ArthurAdmiraal/EISFlowSensing/Documentation/Render/2_2Vtst_24V_Disturb_Screenshot.png

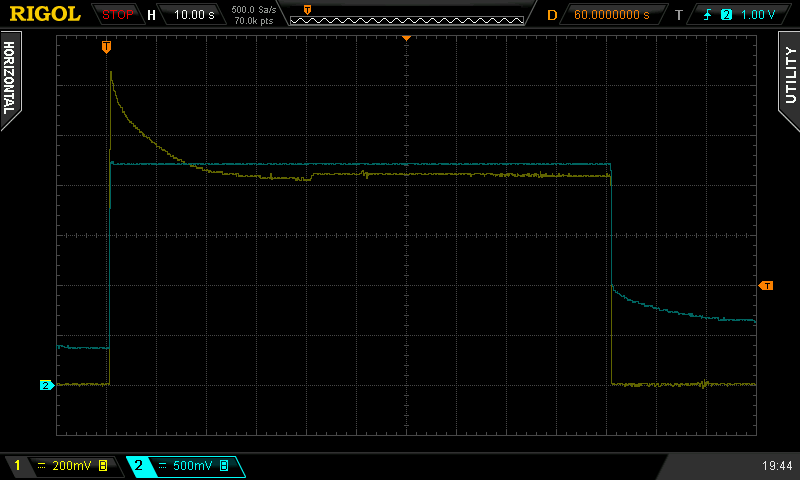
Documentation/Render/2_2Vtst_24V_Disturb_Screenshot.png
