ArthurAdmiraal/EISFlowSensing/Documentation/Render/2_2Vtst_24V_Normal_Screenshot.png

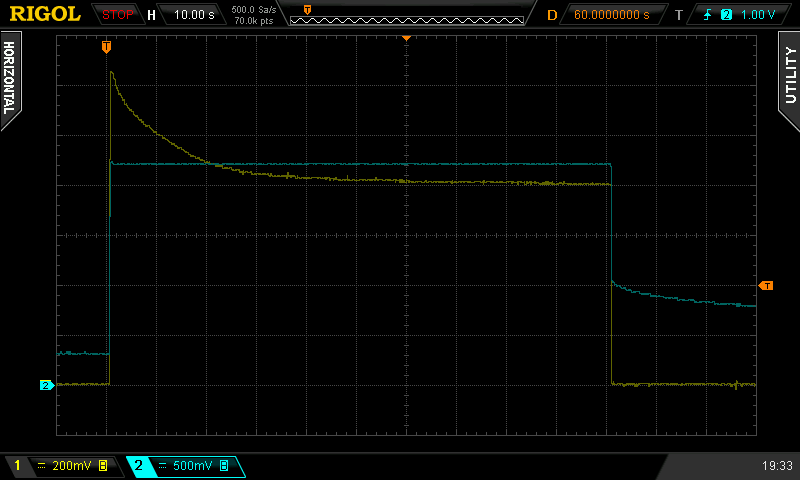
Documentation/Render/2_2Vtst_24V_Normal_Screenshot.png
