ArthurAdmiraal/EISFlowSensing/Documentation/Render/3DPrintGlueing.jpg

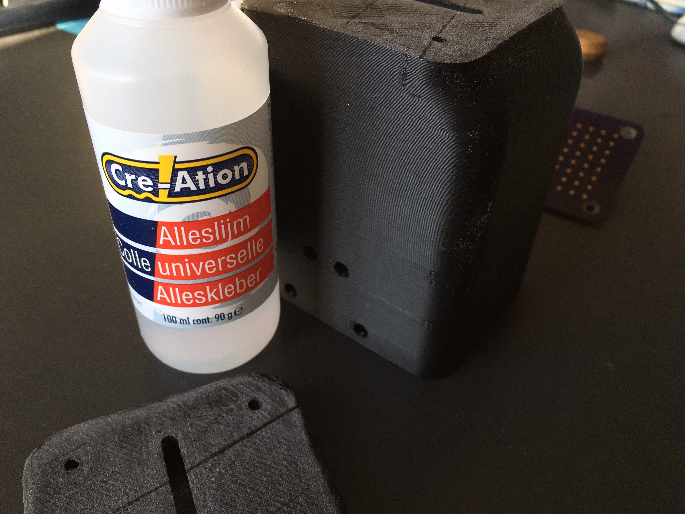
Documentation/Render/3DPrintGlueing.jpg
