ArthurAdmiraal/EISFlowSensing/Documentation/Render/DSC00186.jpg

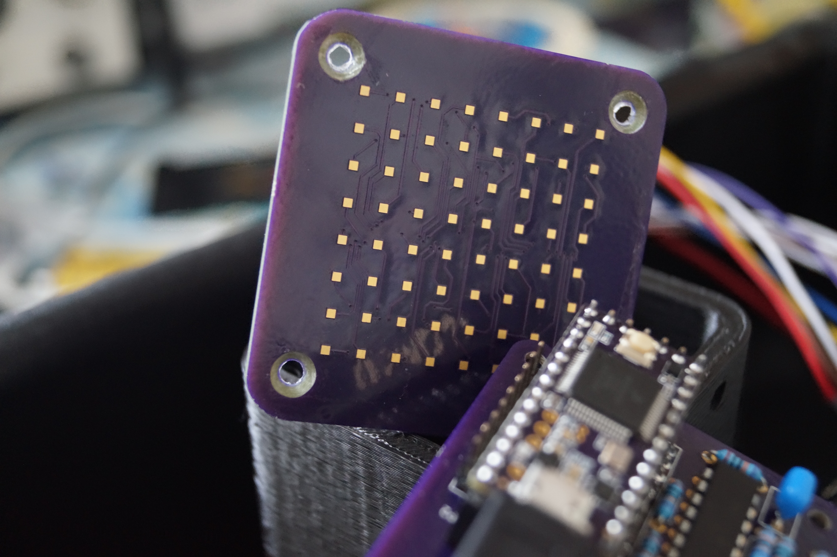
Documentation/Render/DSC00186.jpg
