ArthurAdmiraal/EISFlowSensing/Documentation/Render/DSC00188.jpg

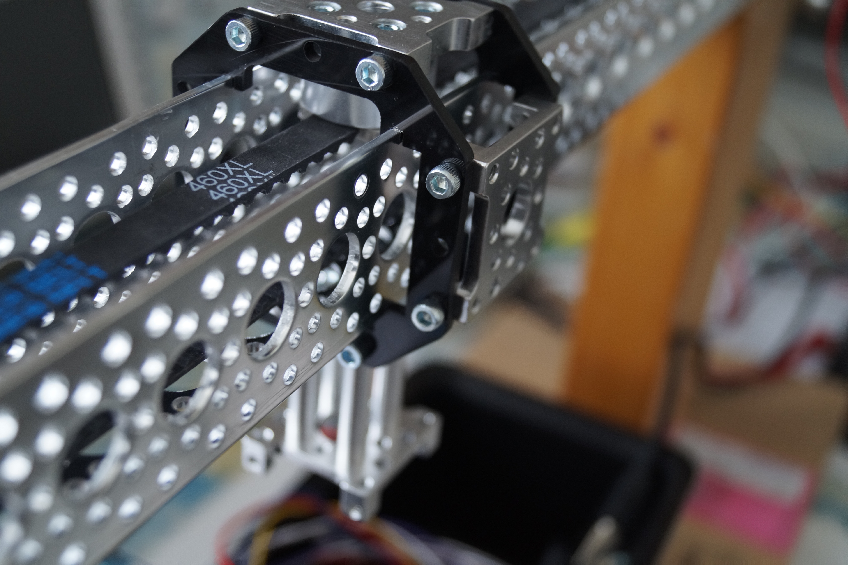
Documentation/Render/DSC00188.jpg
