ArthurAdmiraal/EISFlowSensing/Documentation/Render/ElectrodeAdjacent.png

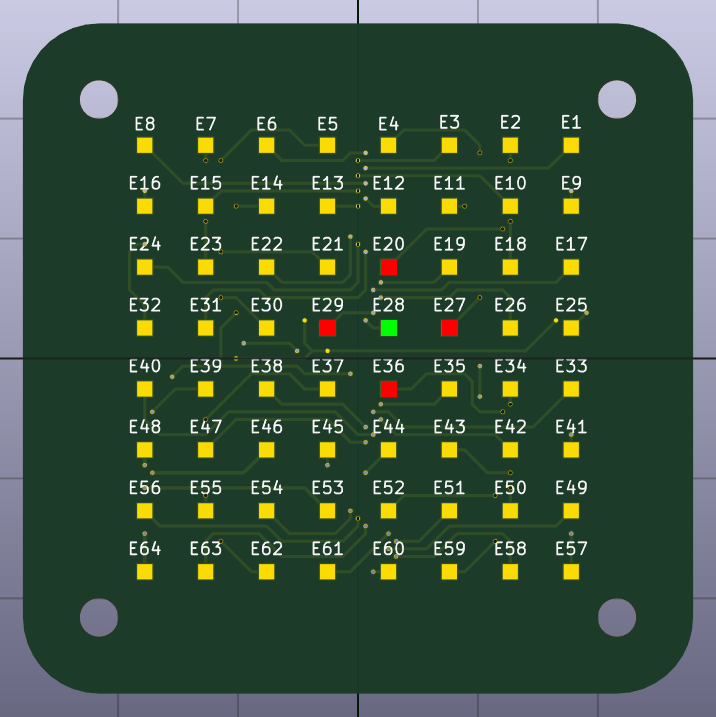
Documentation/Render/ElectrodeAdjacent.png
