ArthurAdmiraal/EISFlowSensing/Documentation/Render/ElectrodeChessBoard.svg.png

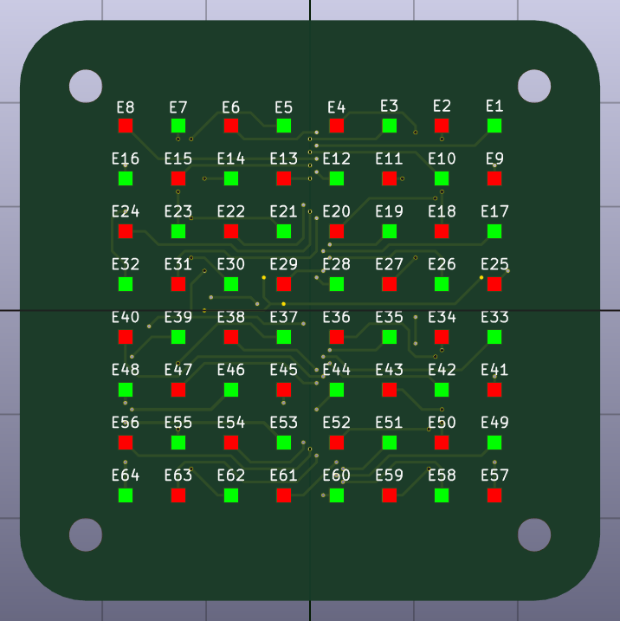
Documentation/Render/ElectrodeChessBoard.svg.png
