ArthurAdmiraal/EISFlowSensing/Documentation/Render/ElectrolyticSolution.png

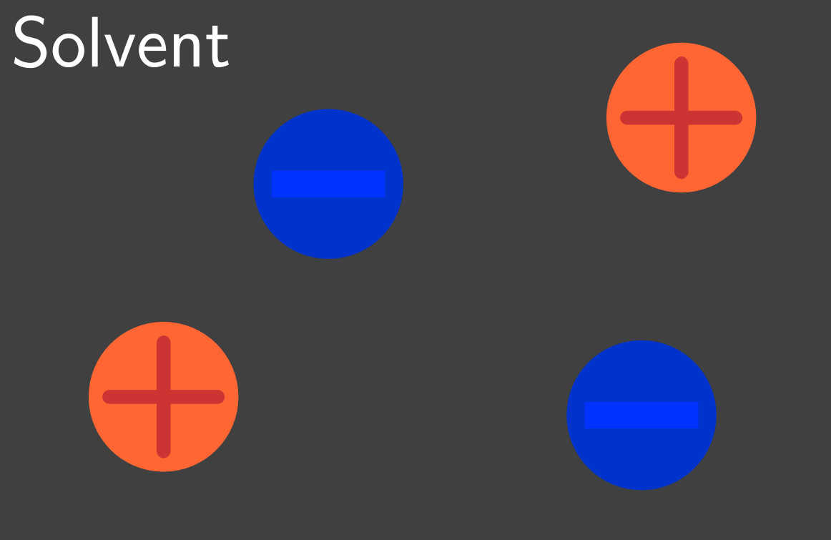
Documentation/Render/ElectrolyticSolution.png
