ArthurAdmiraal/EISFlowSensing/Documentation/Render/EquivalentCircuit.png

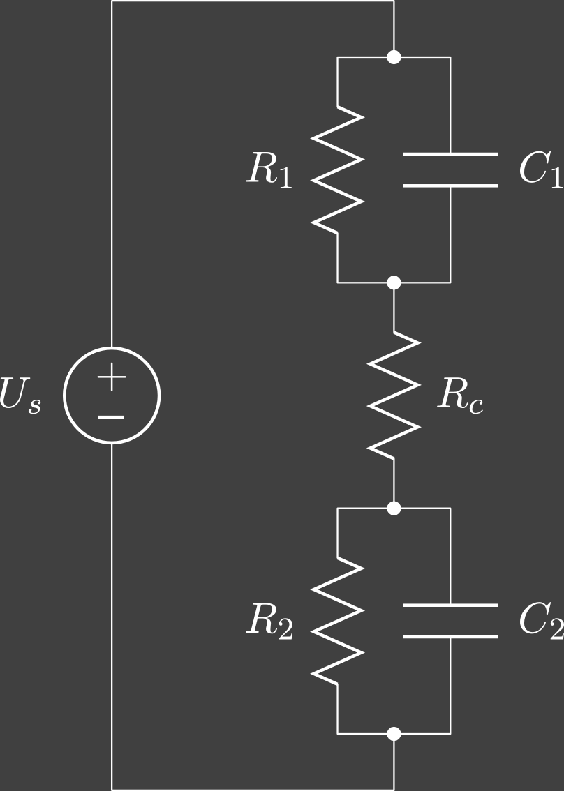
Documentation/Render/EquivalentCircuit.png
