ArthurAdmiraal/EISFlowSensing/Documentation/Render/FaradaicCurrent.png

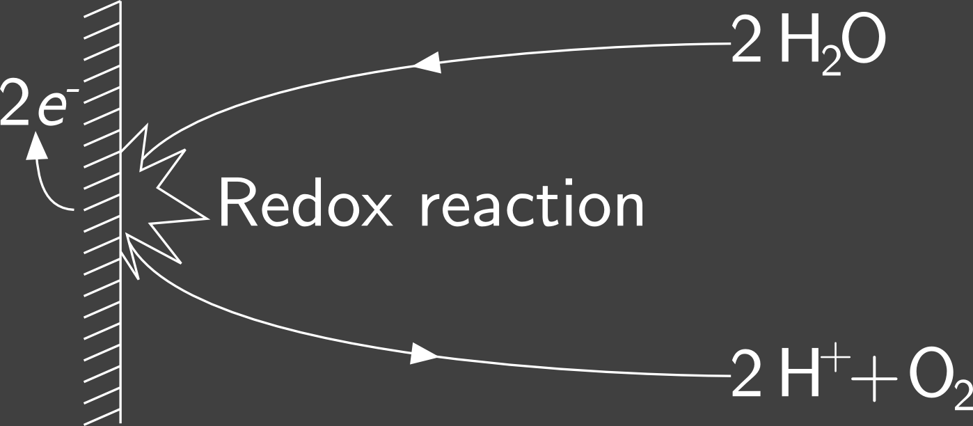
Documentation/Render/FaradaicCurrent.png
