ArthurAdmiraal/EISFlowSensing/Documentation/Render/GrubScrew.jpg

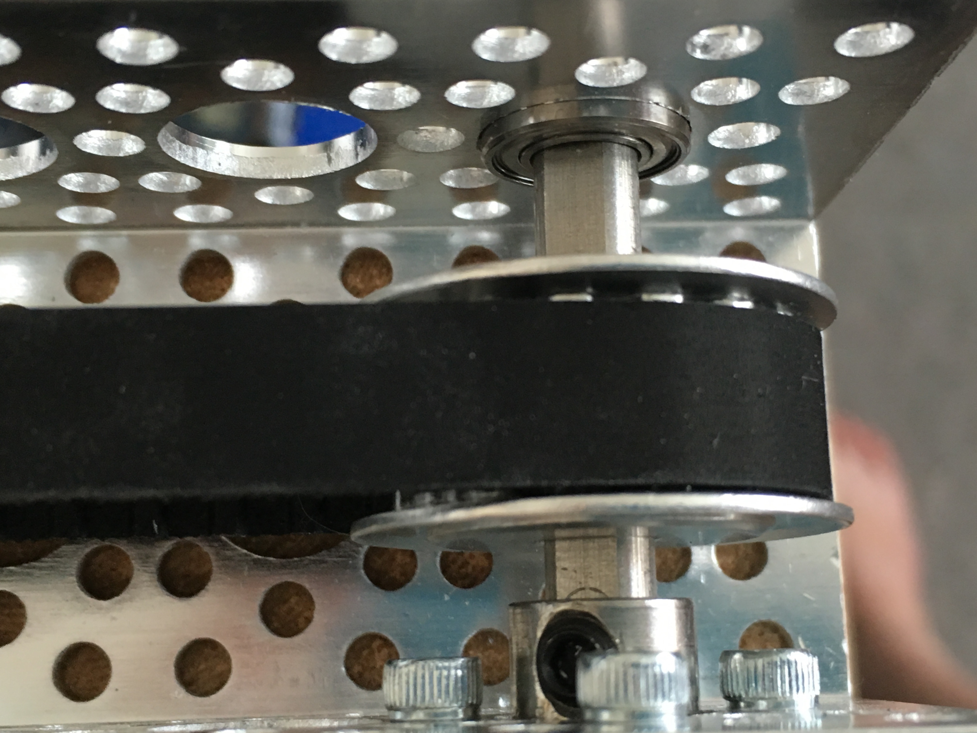
Documentation/Render/GrubScrew.jpg
