ArthurAdmiraal/EISFlowSensing/Documentation/Render/IMG_5456.jpg

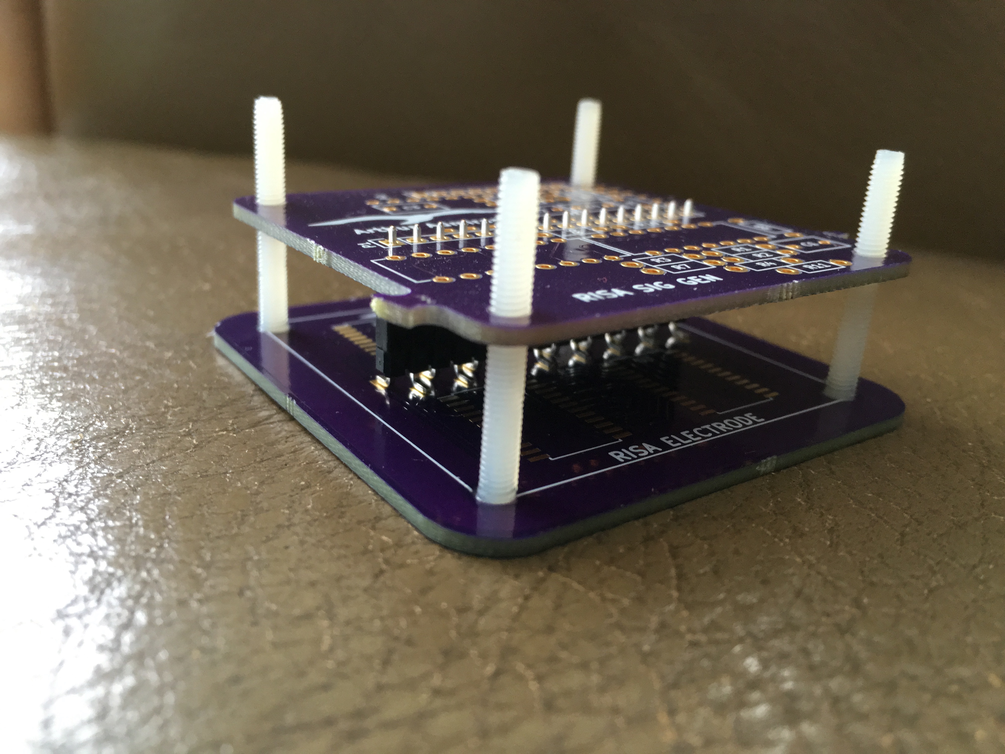
Documentation/Render/IMG_5456.jpg
