ArthurAdmiraal/EISFlowSensing/Documentation/Render/IMG_5630.JPG

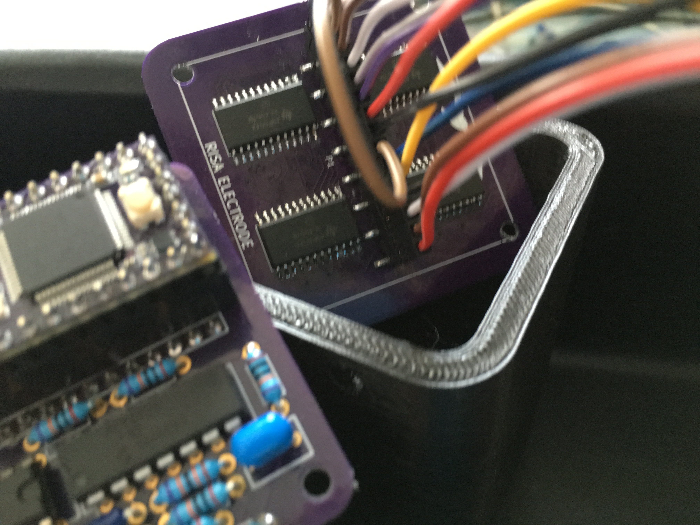
Documentation/Render/IMG_5630.JPG
