ArthurAdmiraal/EISFlowSensing/Documentation/Render/LimitSwitch.jpg

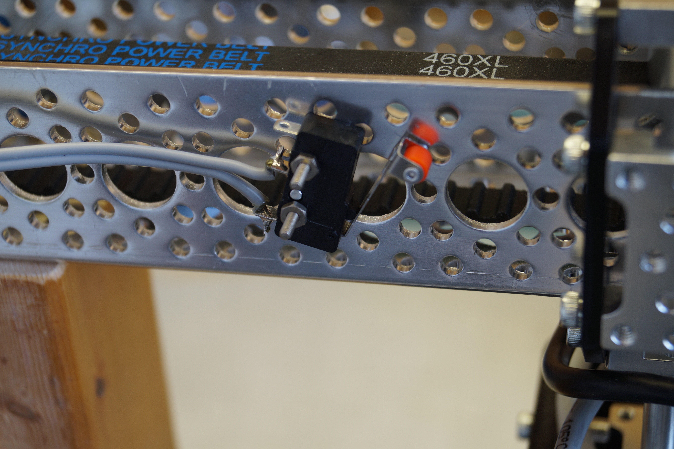
Documentation/Render/LimitSwitch.jpg
