ArthurAdmiraal/EISFlowSensing/Documentation/Render/LimitSwitchCableHotGlue.jpg

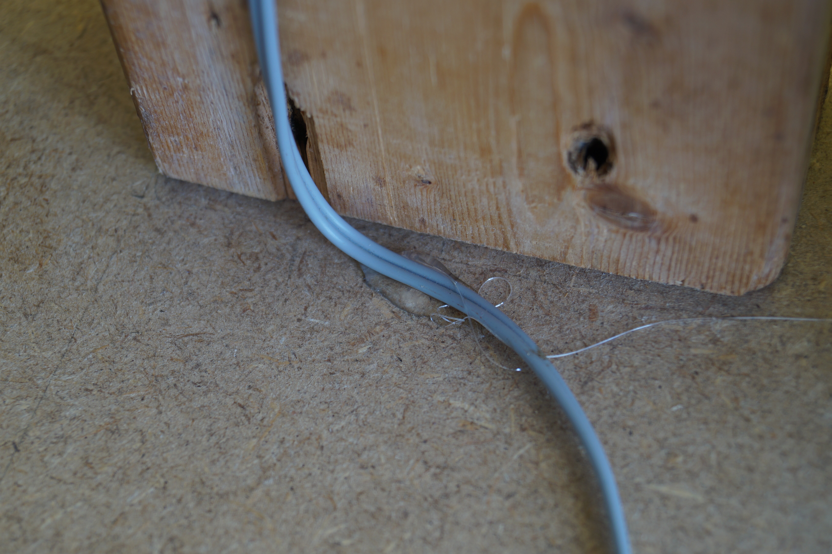
Documentation/Render/LimitSwitchCableHotGlue.jpg
