ArthurAdmiraal/EISFlowSensing/Documentation/Render/ORingUnfit.jpg

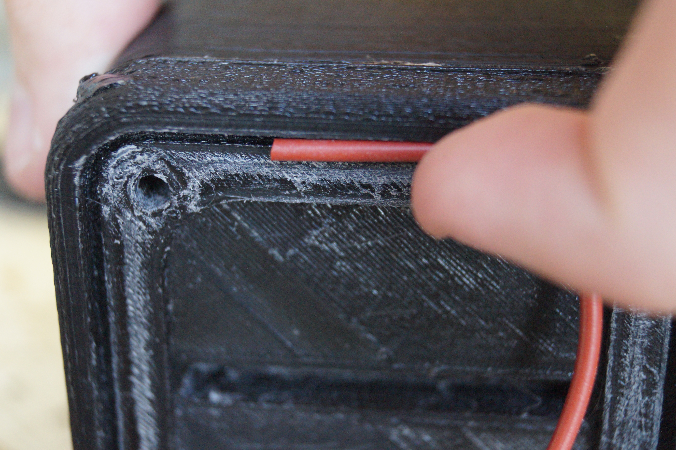
Documentation/Render/ORingUnfit.jpg
