ArthurAdmiraal/EISFlowSensing/Documentation/Render/RISA_Case_CentralShaft.png

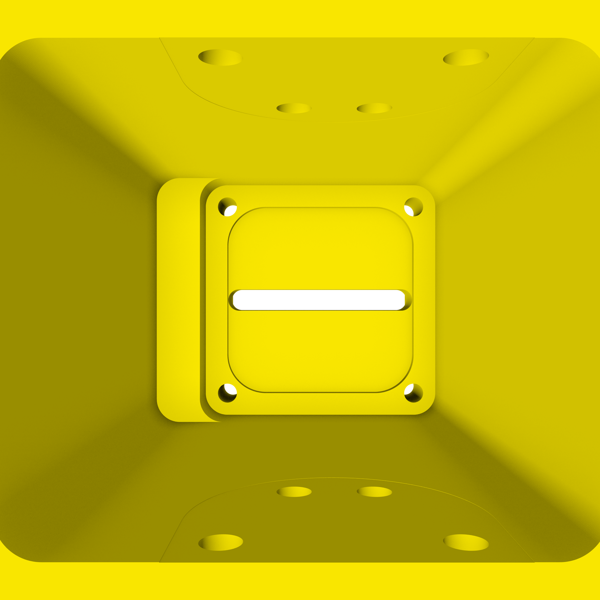
Documentation/Render/RISA_Case_CentralShaft.png
