ArthurAdmiraal/EISFlowSensing/Documentation/Render/RISA_Case_ElectrodeMount.png

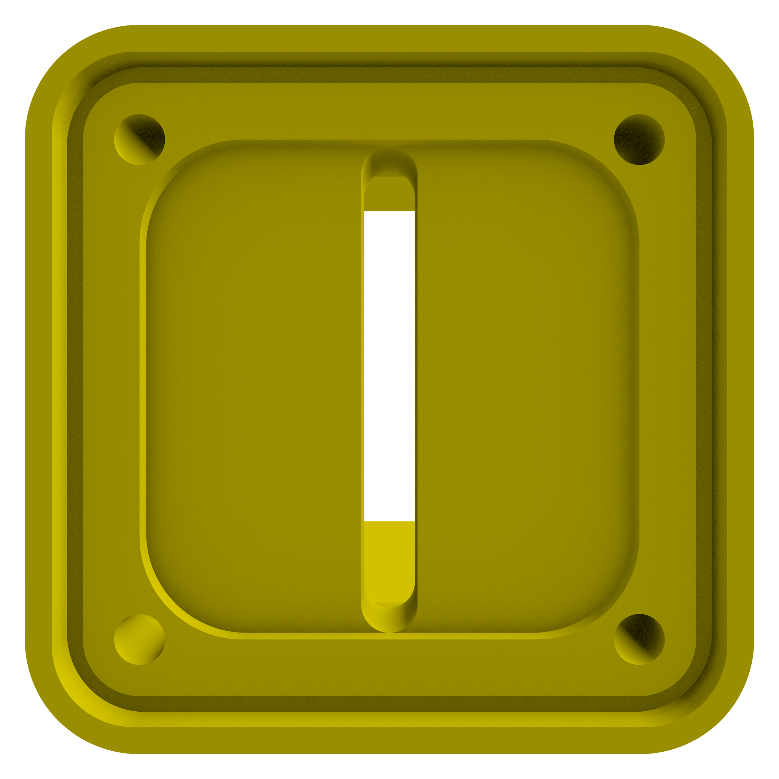
Documentation/Render/RISA_Case_ElectrodeMount.png
