ArthurAdmiraal/EISFlowSensing/Documentation/Render/RISA_Case_full.png

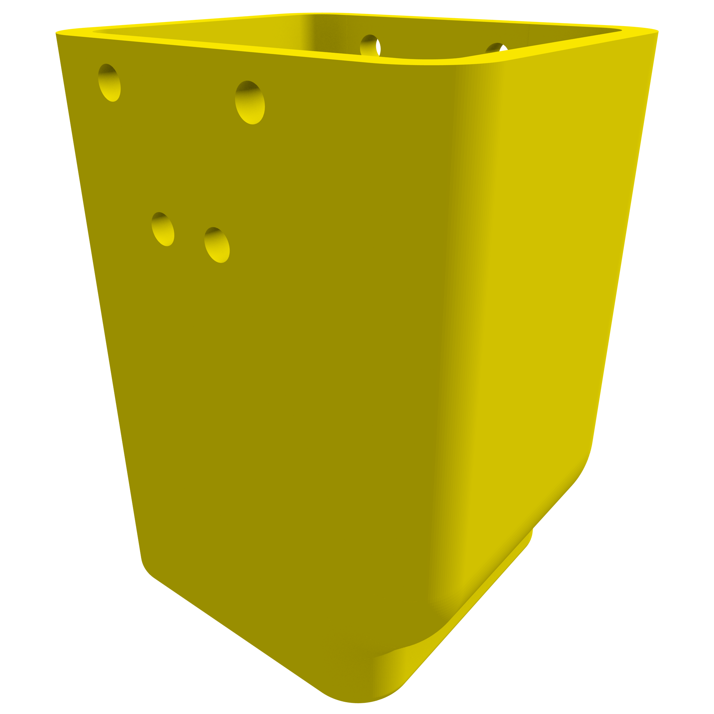
Documentation/Render/RISA_Case_full.png
