ArthurAdmiraal/EISFlowSensing/Documentation/Render/RISA_Case_MountingHoles.png

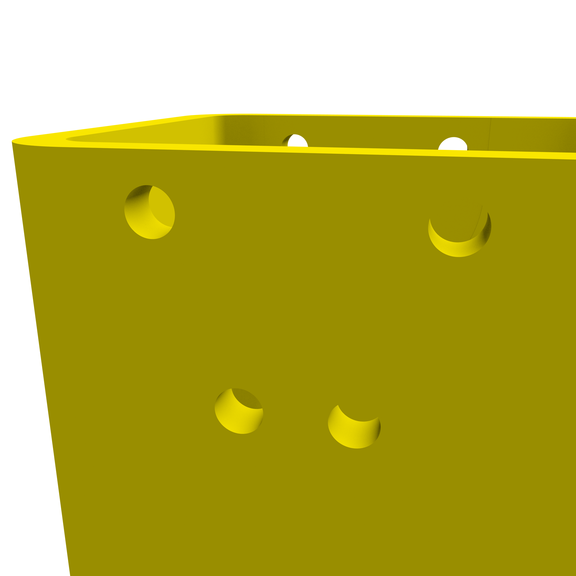
Documentation/Render/RISA_Case_MountingHoles.png
