ArthurAdmiraal/EISFlowSensing/Documentation/Render/RisaSliderInterface.jpg

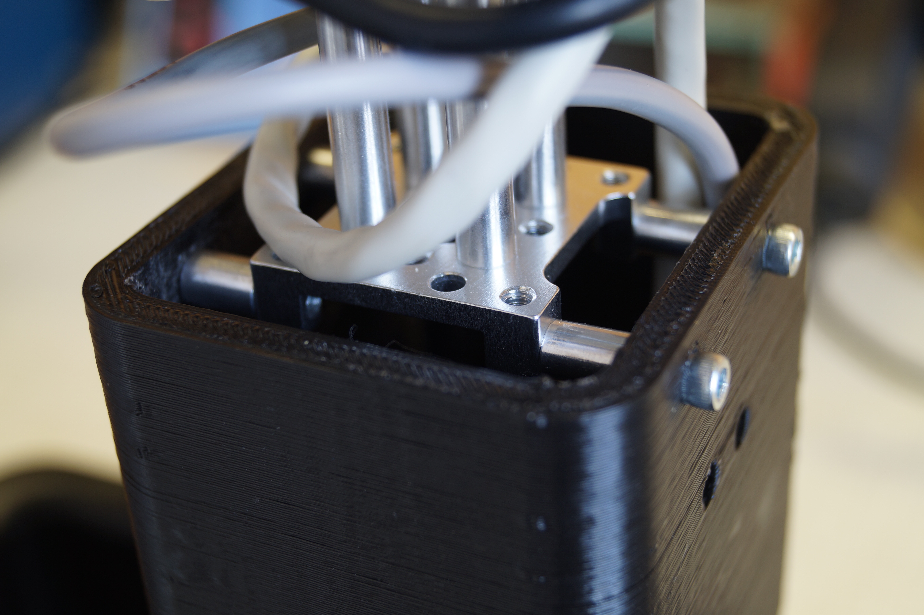
Documentation/Render/RisaSliderInterface.jpg
