ArthurAdmiraal/EISFlowSensing/Documentation/Render/SigGenCurrentBuffer.png

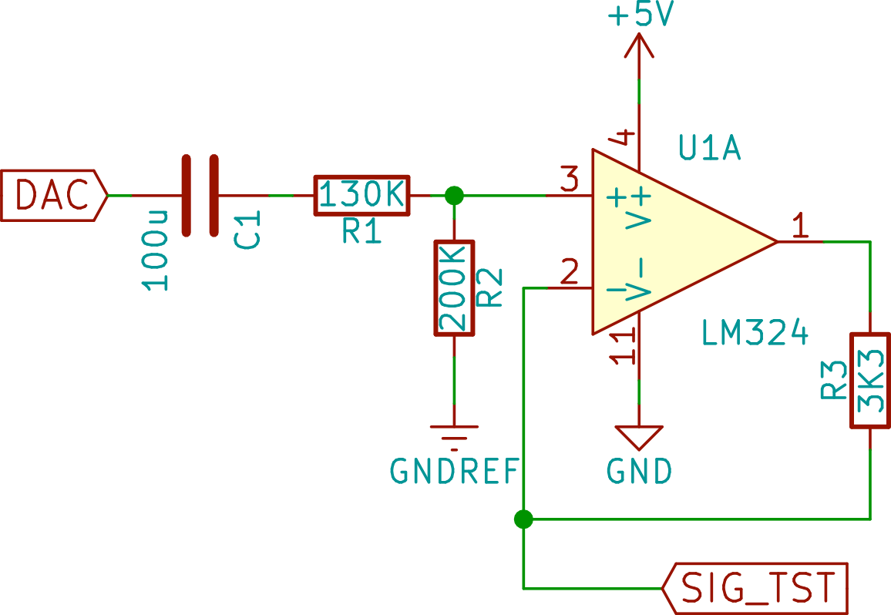
Documentation/Render/SigGenCurrentBuffer.png
