ArthurAdmiraal/EISFlowSensing/Documentation/Render/SigGenFinal.png

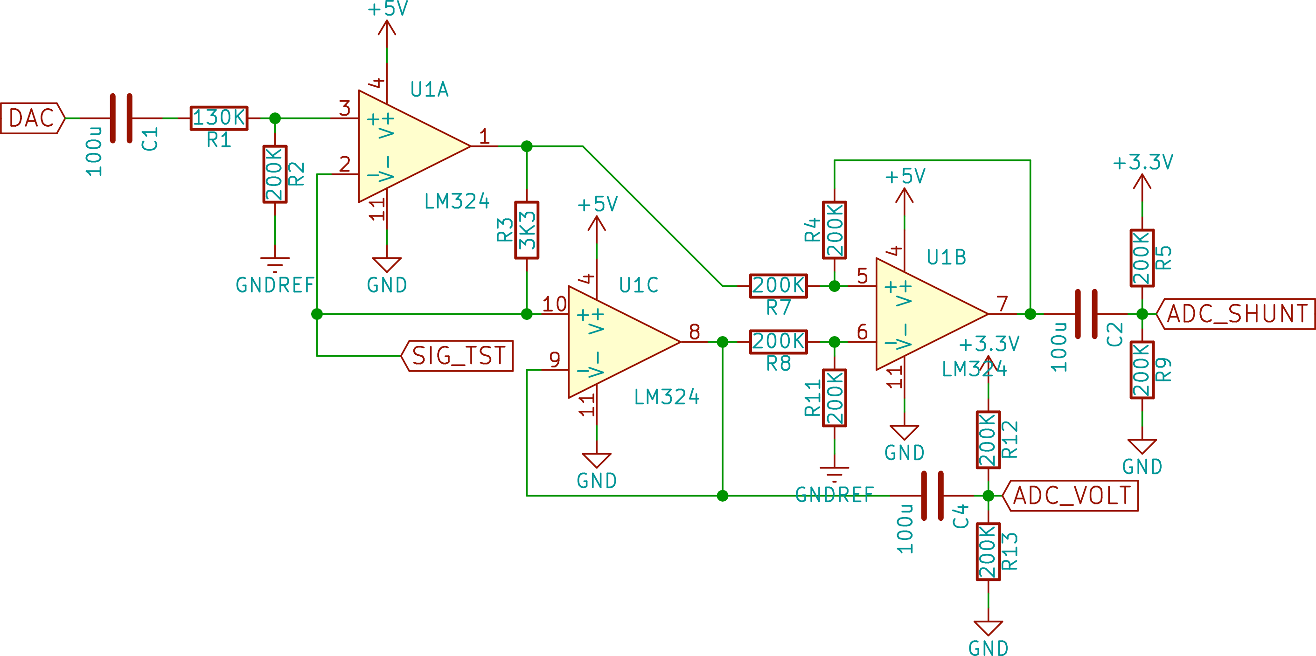
Documentation/Render/SigGenFinal.png
