ArthurAdmiraal/EISFlowSensing/Documentation/Render/SigGenInputBiasing.png

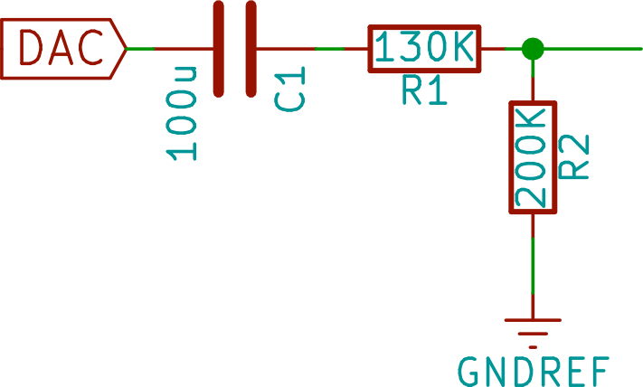
Documentation/Render/SigGenInputBiasing.png
