ArthurAdmiraal/EISFlowSensing/Documentation/Render/SigGenMultiplexer.png

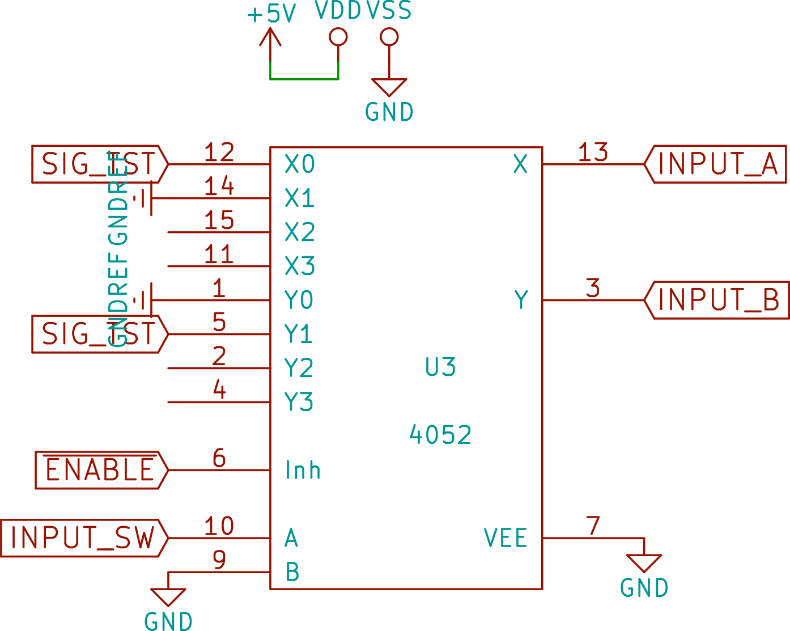
Documentation/Render/SigGenMultiplexer.png
