ArthurAdmiraal/EISFlowSensing/Documentation/Render/SigGenTeensy.png

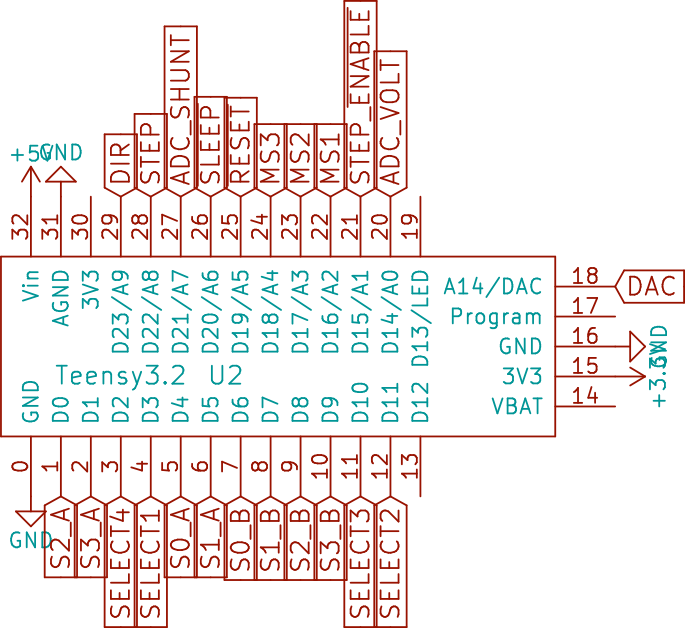
Documentation/Render/SigGenTeensy.png
