ArthurAdmiraal/EISFlowSensing/Documentation/Render/SigGenVirtualGround.png

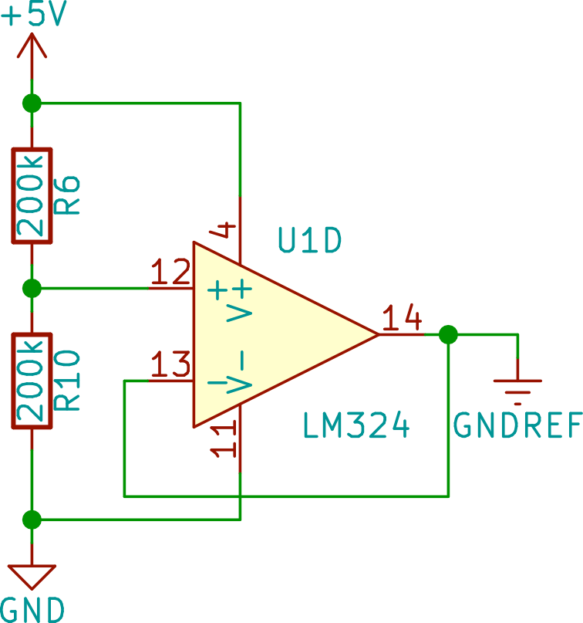
Documentation/Render/SigGenVirtualGround.png
