ArthurAdmiraal/EISFlowSensing/Documentation/Render/Slider.jpg

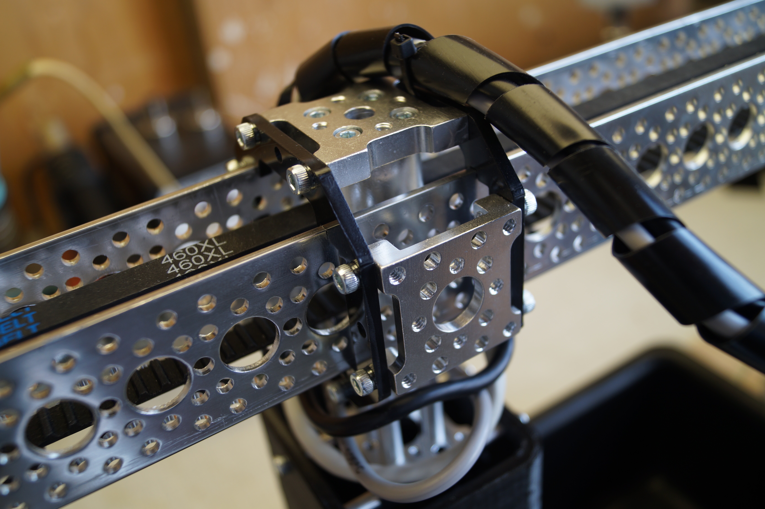
Documentation/Render/Slider.jpg
