ArthurAdmiraal/EISFlowSensing/Documentation/Render/SliderBaseInterface.jpg

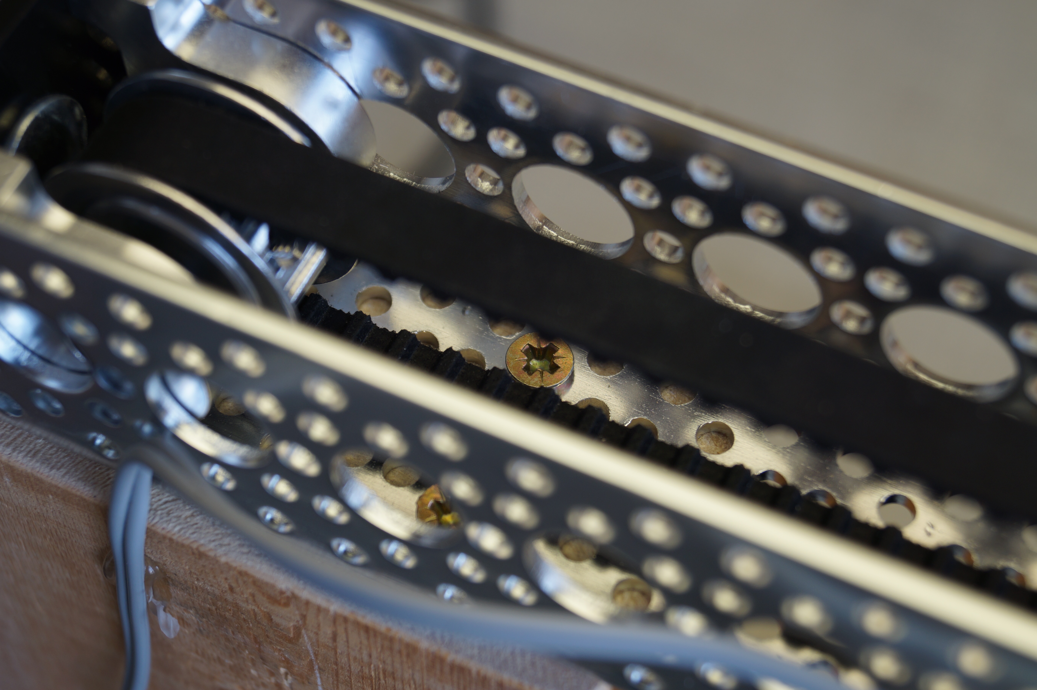
Documentation/Render/SliderBaseInterface.jpg
