ArthurAdmiraal/EISFlowSensing/Documentation/Render/StepperMotor.jpg

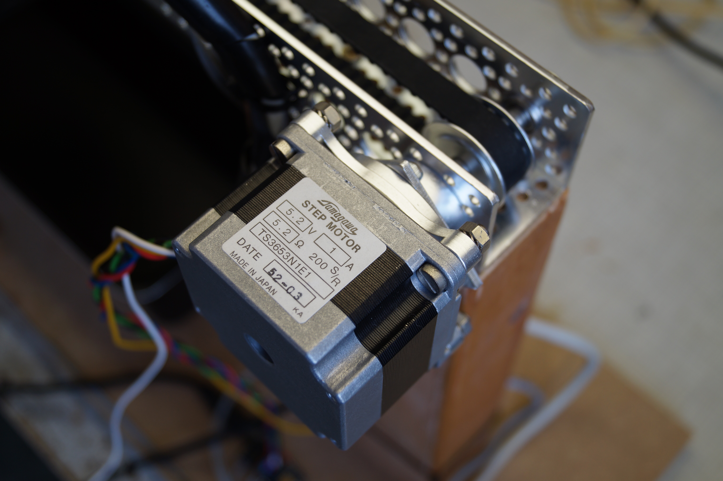
Documentation/Render/StepperMotor.jpg
