ArthurAdmiraal/EISFlowSensing/Documentation/Render/StepperMotorDriver.jpg

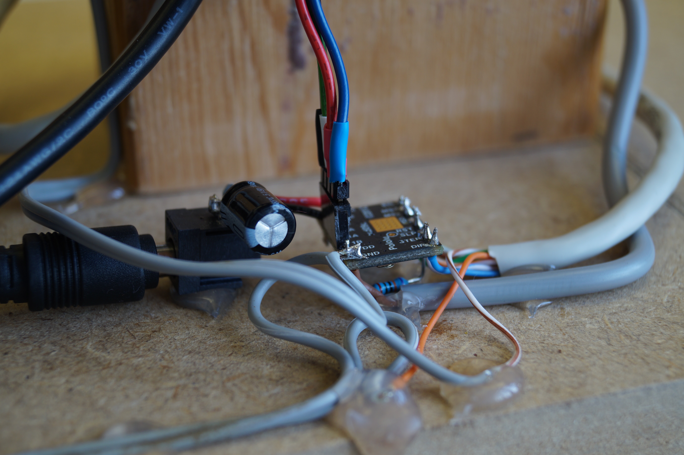
Documentation/Render/StepperMotorDriver.jpg
