ArthurAdmiraal/EISFlowSensing/Documentation/Render/WeightMonitoring.png

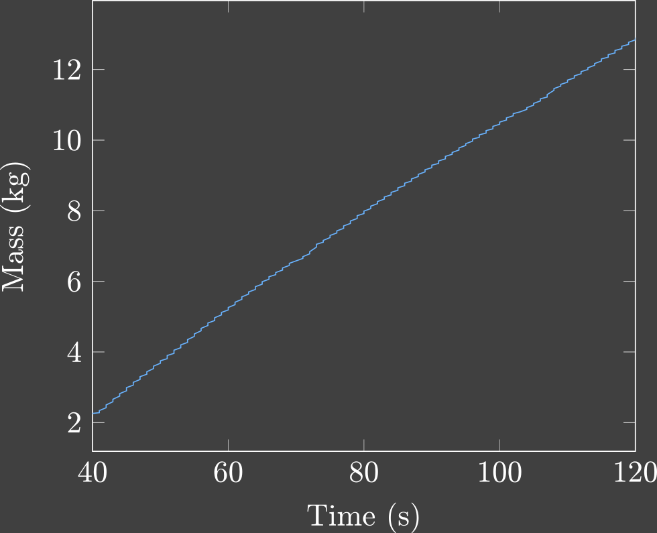
Documentation/Render/WeightMonitoring.png
