ArthurAdmiraal/EISFlowSensing/Documentation/Source/BodgeWire.jpg

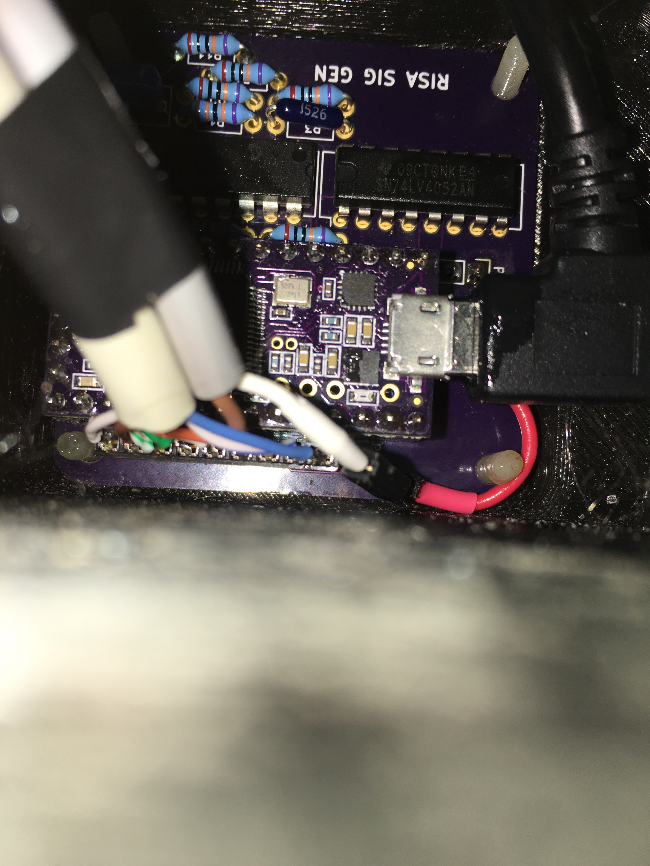
Documentation/Source/BodgeWire.jpg
