ArthurAdmiraal/EISFlowSensing/Documentation/Build_instructions/Step1.PNG

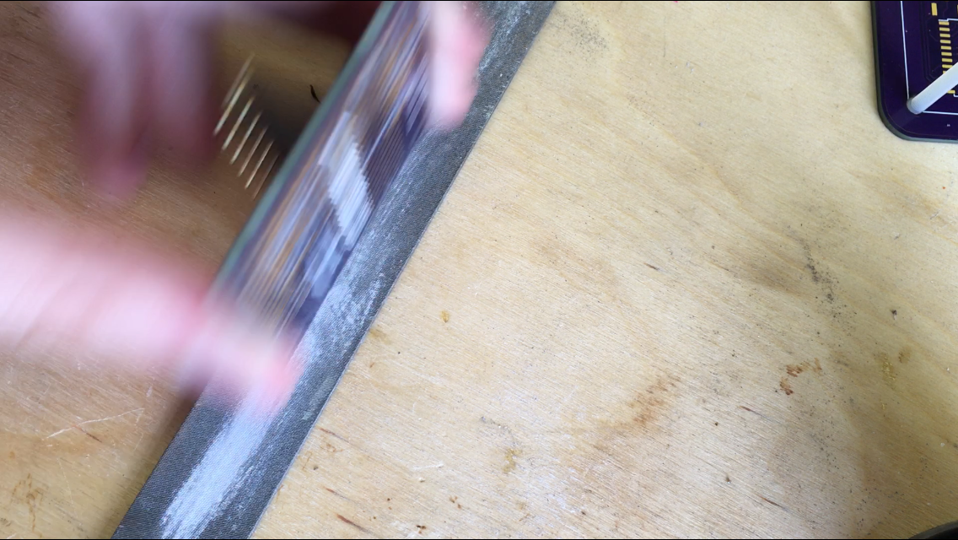
Documentation/Build_instructions/Step1.PNG
