ArthurAdmiraal/EISFlowSensing/Documentation/Build_instructions/Step1_0.PNG

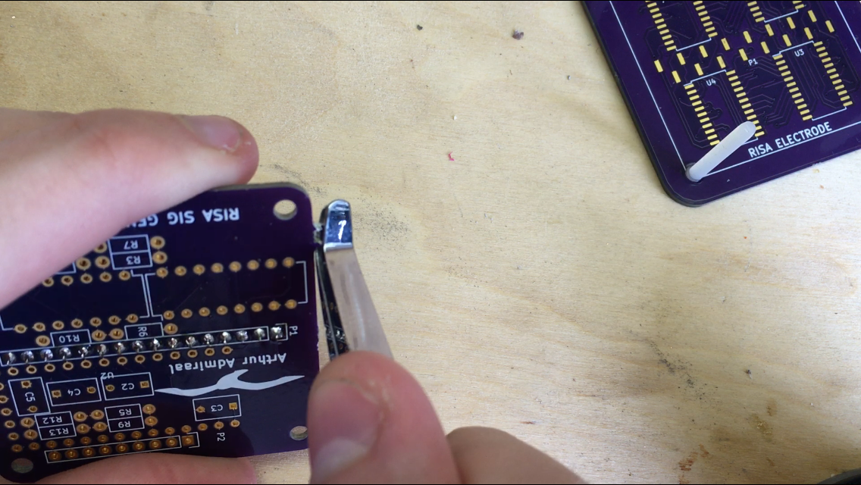
Documentation/Build_instructions/Step1_0.PNG
