ArthurAdmiraal/EISFlowSensing/Documentation/Build_instructions/Step2.PNG

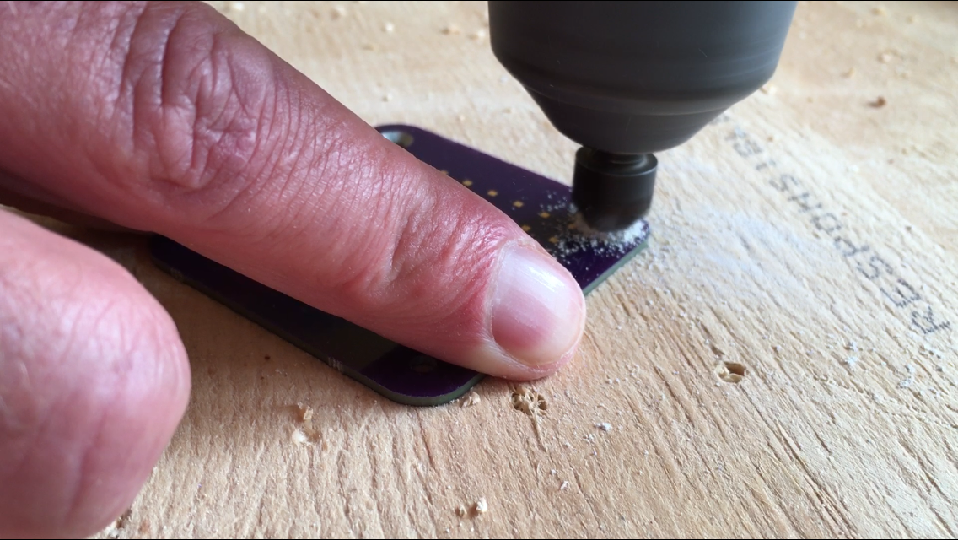
Documentation/Build_instructions/Step2.PNG
