ArthurAdmiraal/EISFlowSensing/Documentation/Build_instructions/Step3_1.PNG

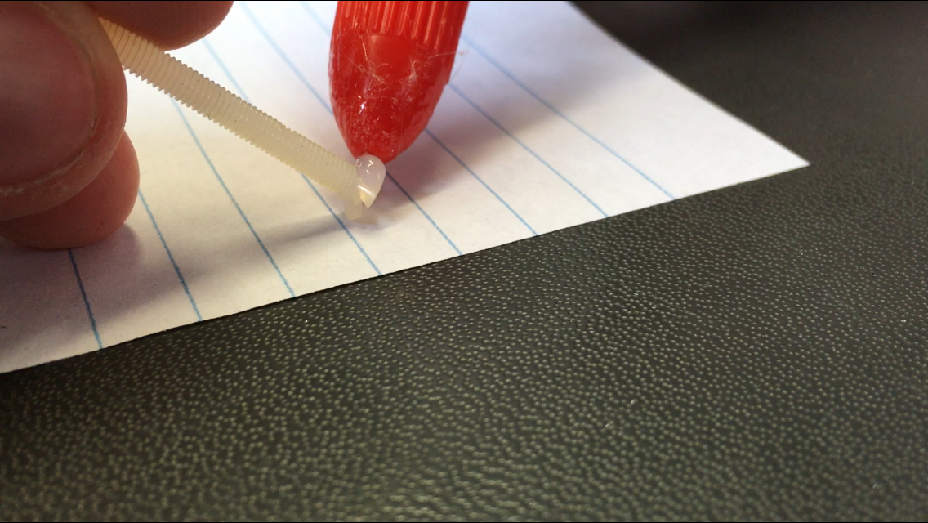
Documentation/Build_instructions/Step3_1.PNG
