ArthurAdmiraal/EISFlowSensing/Documentation/Build_instructions/Step3_2.PNG

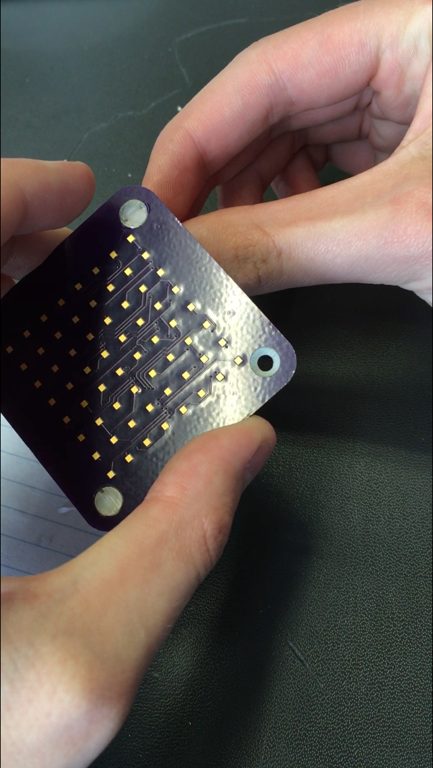
Documentation/Build_instructions/Step3_2.PNG
