ArthurAdmiraal/EISFlowSensing/Documentation/Build_instructions/Step3_3.JPG

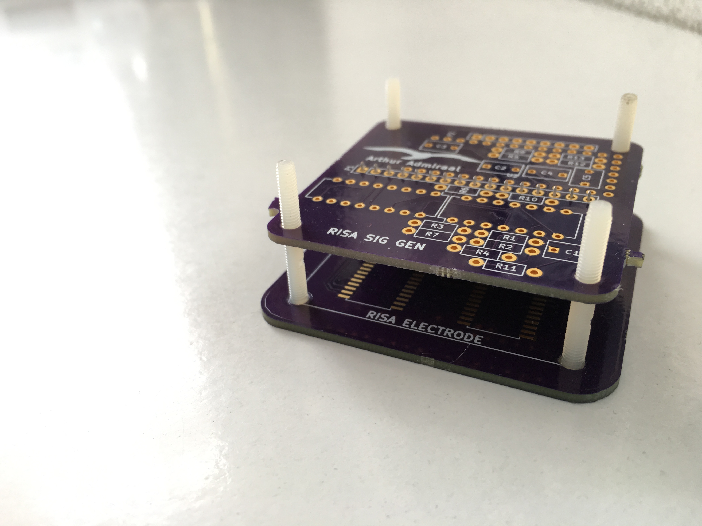
Documentation/Build_instructions/Step3_3.JPG
