ArthurAdmiraal/EISFlowSensing/Documentation/Build_instructions/Step4_1.PNG

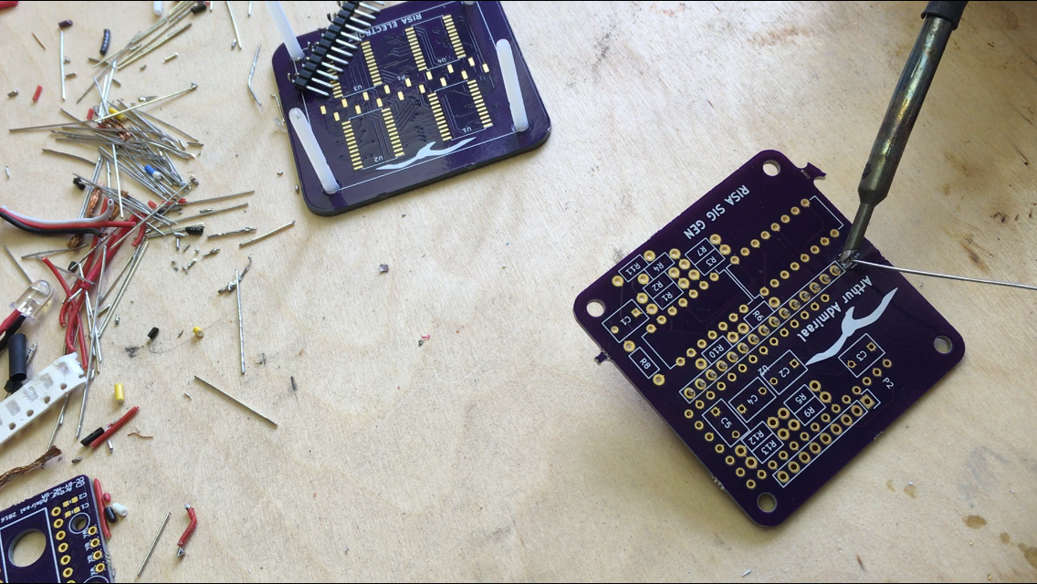
Documentation/Build_instructions/Step4_1.PNG
