ArthurAdmiraal/EISFlowSensing/Documentation/Build_instructions/Step4_2.PNG

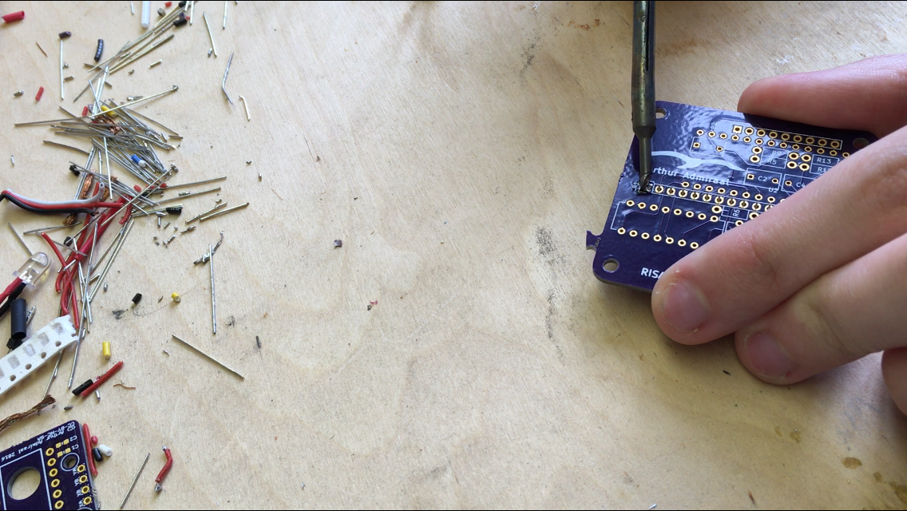
Documentation/Build_instructions/Step4_2.PNG
