ArthurAdmiraal/EISFlowSensing/Documentation/Build_instructions/Step4_3.PNG

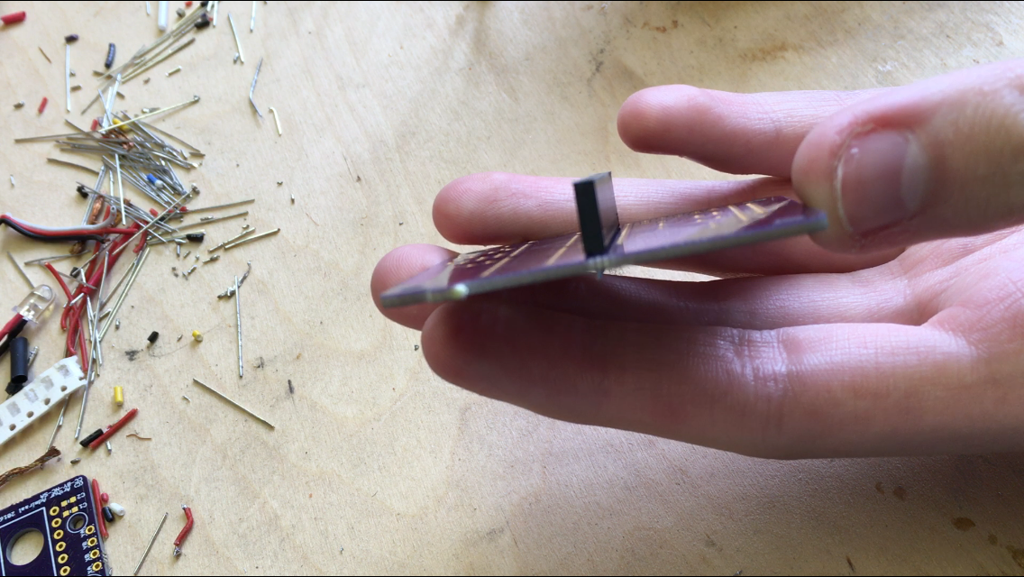
Documentation/Build_instructions/Step4_3.PNG
