ArthurAdmiraal/EISFlowSensing/Documentation/Build_instructions/Step4_4.PNG

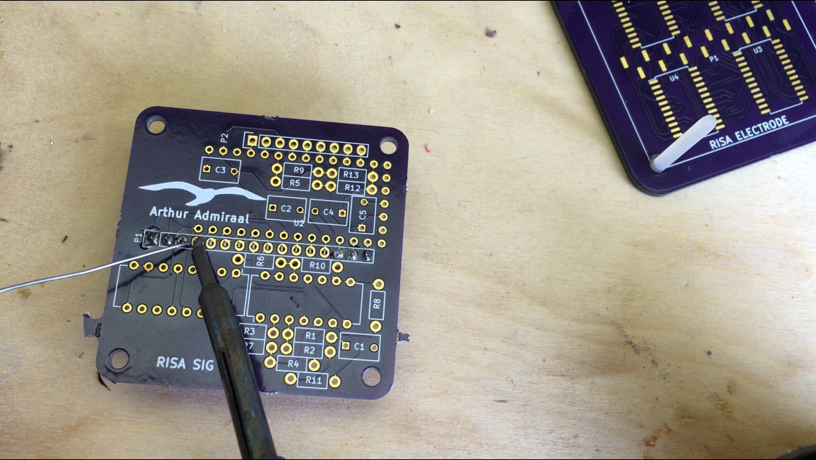
Documentation/Build_instructions/Step4_4.PNG
