ArthurAdmiraal/EISFlowSensing/Documentation/Build_instructions/Step5_1.PNG

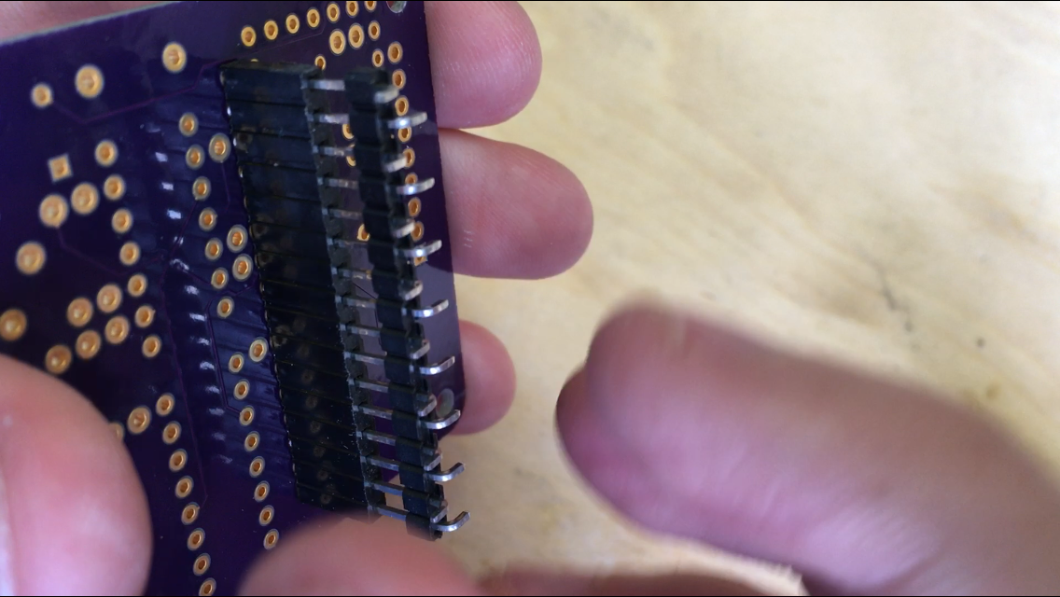
Documentation/Build_instructions/Step5_1.PNG
