ArthurAdmiraal/EISFlowSensing/Documentation/Build_instructions/Step5_2.PNG

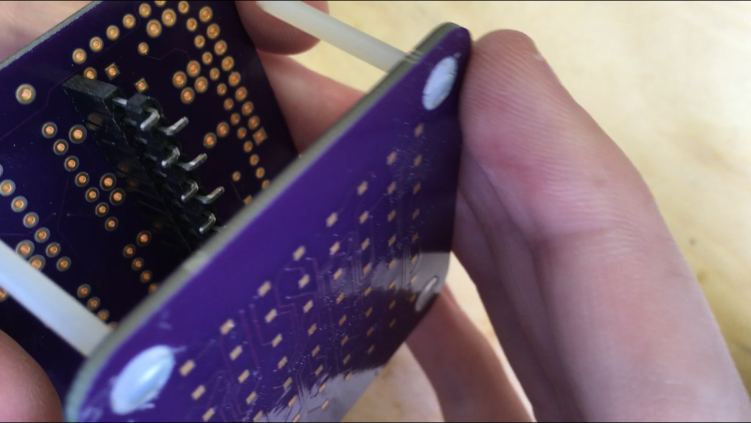
Documentation/Build_instructions/Step5_2.PNG
