ArthurAdmiraal/EISFlowSensing/Documentation/Build_instructions/Step5_3.PNG

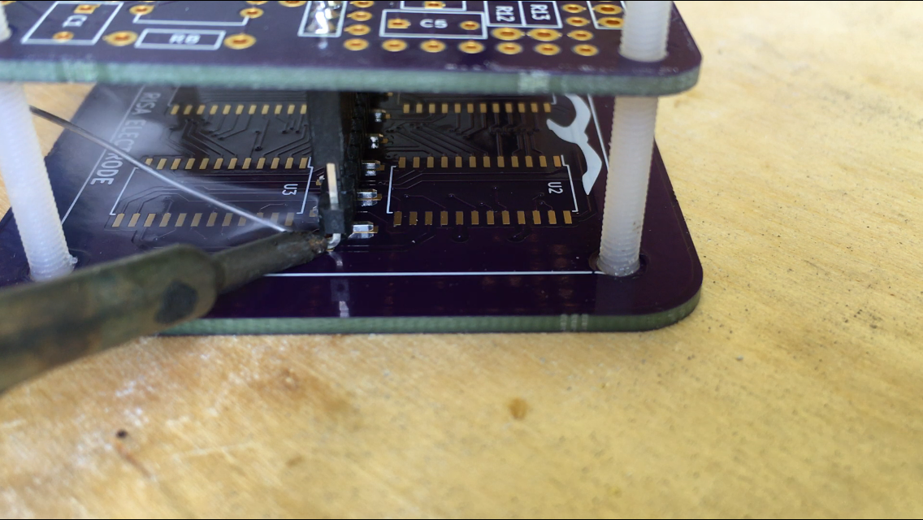
Documentation/Build_instructions/Step5_3.PNG
