ArthurAdmiraal/EISFlowSensing/Documentation/Build_instructions/Step5_4.PNG

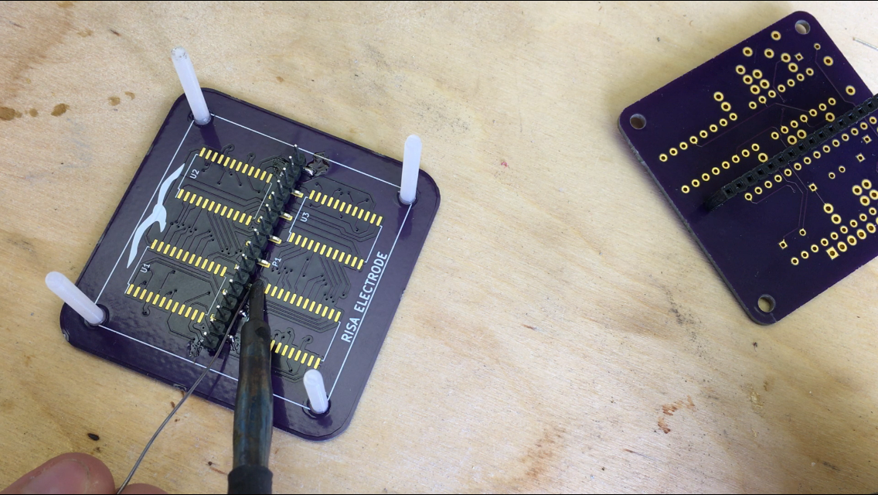
Documentation/Build_instructions/Step5_4.PNG
