ArthurAdmiraal/EISFlowSensing/Documentation/Build_instructions/Step6_1.PNG

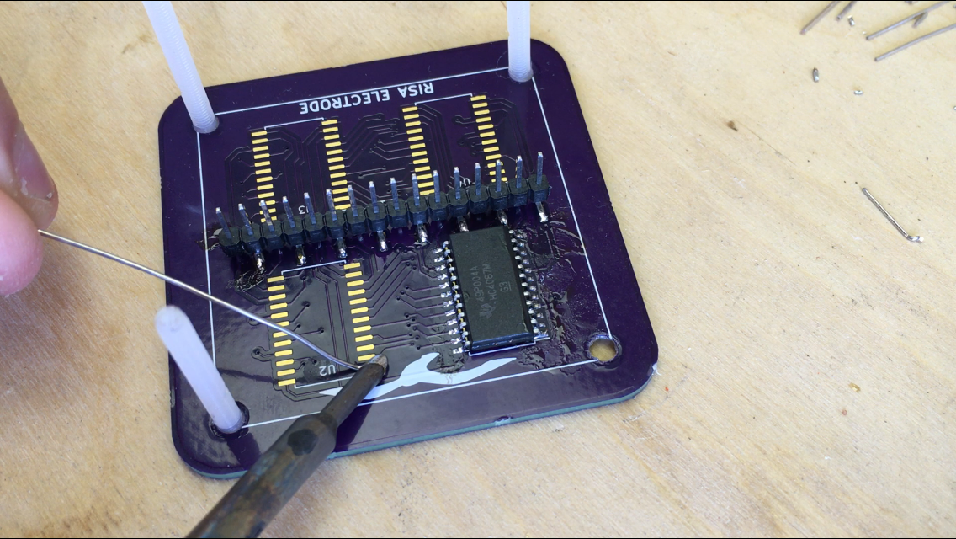
Documentation/Build_instructions/Step6_1.PNG
