ArthurAdmiraal/EISFlowSensing/Documentation/Build_instructions/Step6_2.PNG

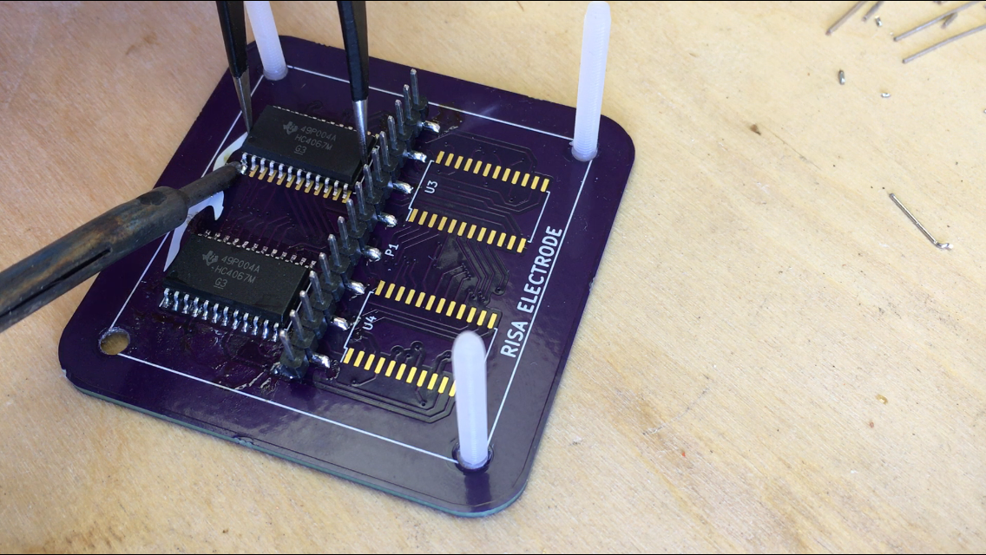
Documentation/Build_instructions/Step6_2.PNG
