ArthurAdmiraal/EISFlowSensing/Documentation/Build_instructions/Step6_3.PNG

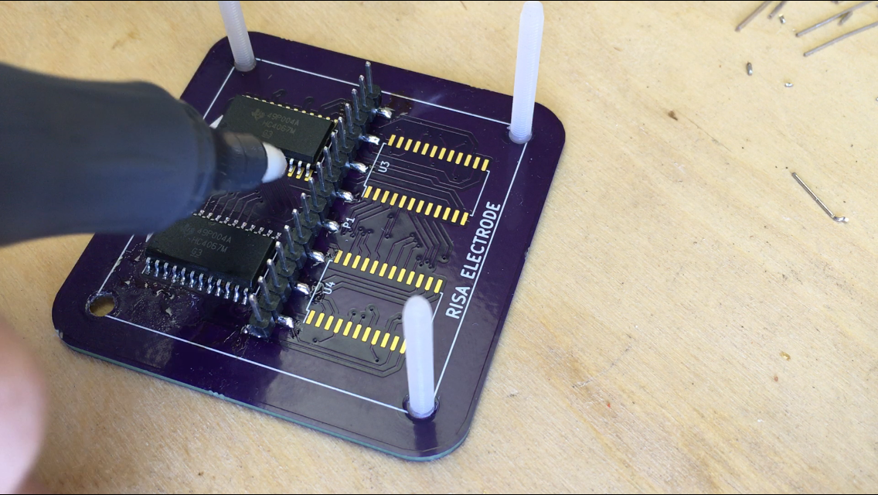
Documentation/Build_instructions/Step6_3.PNG
