ArthurAdmiraal/EISFlowSensing/Documentation/Build_instructions/Step6_4.PNG

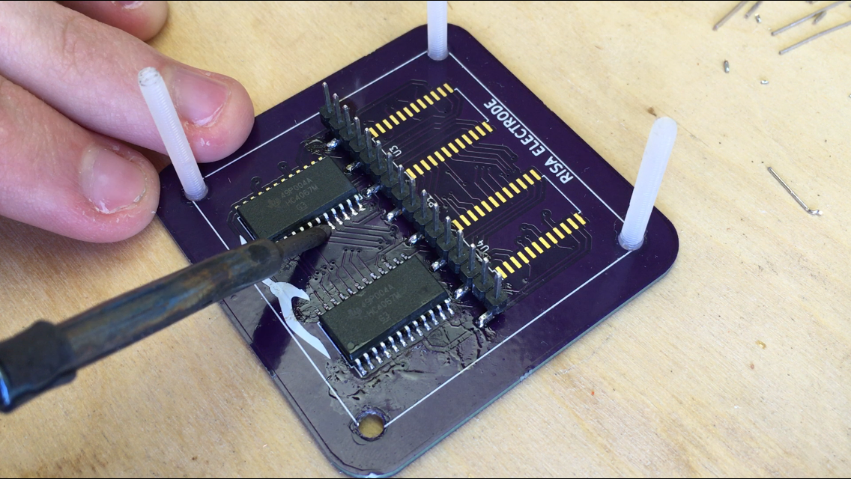
Documentation/Build_instructions/Step6_4.PNG
