ArthurAdmiraal/EISFlowSensing/Documentation/Build_instructions/Step6_5.PNG

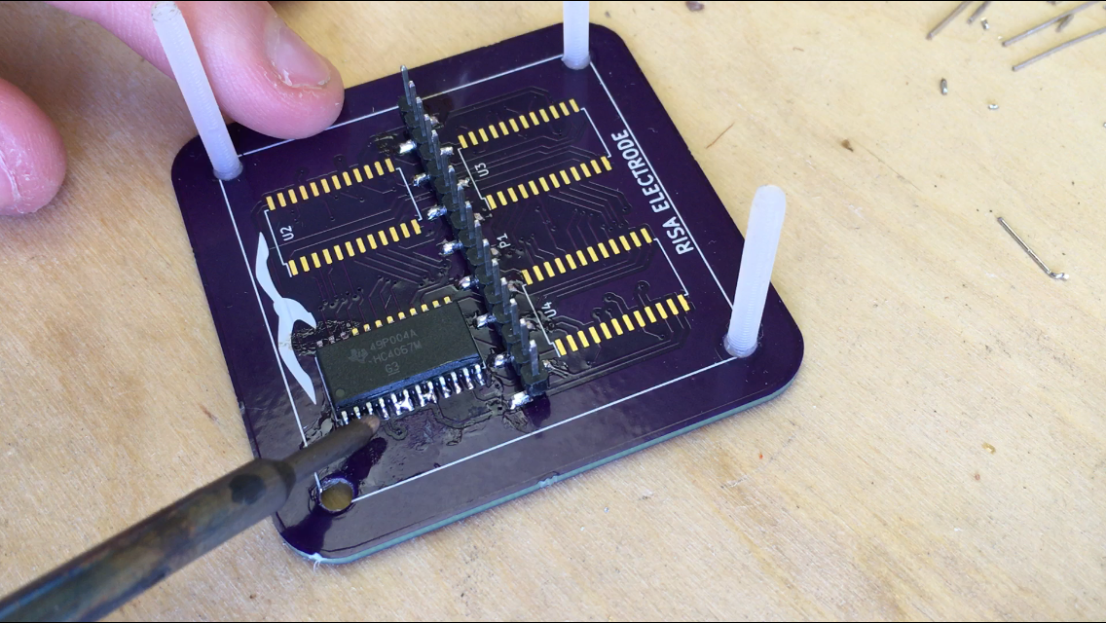
Documentation/Build_instructions/Step6_5.PNG
