ArthurAdmiraal/EISFlowSensing/Documentation/Build_instructions/Step6_6.PNG

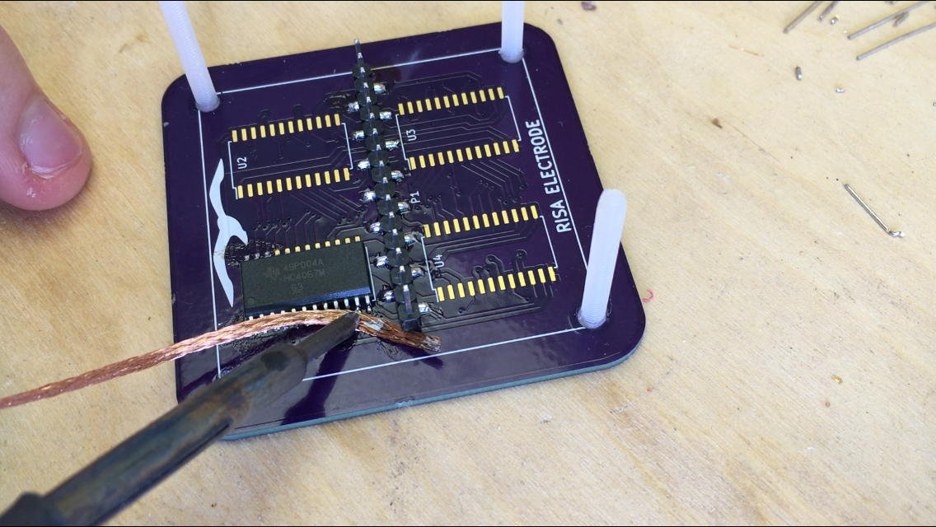
Documentation/Build_instructions/Step6_6.PNG
