ArthurAdmiraal/EISFlowSensing/Documentation/Build_instructions/Step6_7.PNG

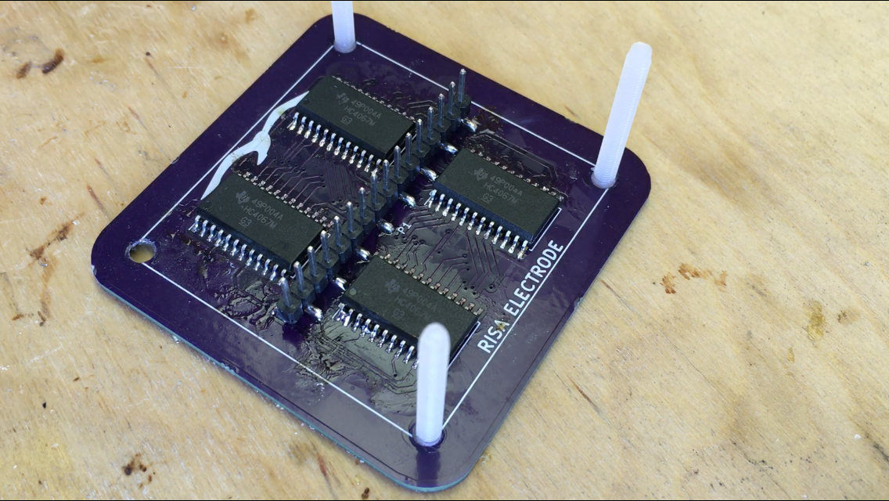
Documentation/Build_instructions/Step6_7.PNG
