ArthurAdmiraal/EISFlowSensing/Documentation/Build_instructions/Step7_1.PNG

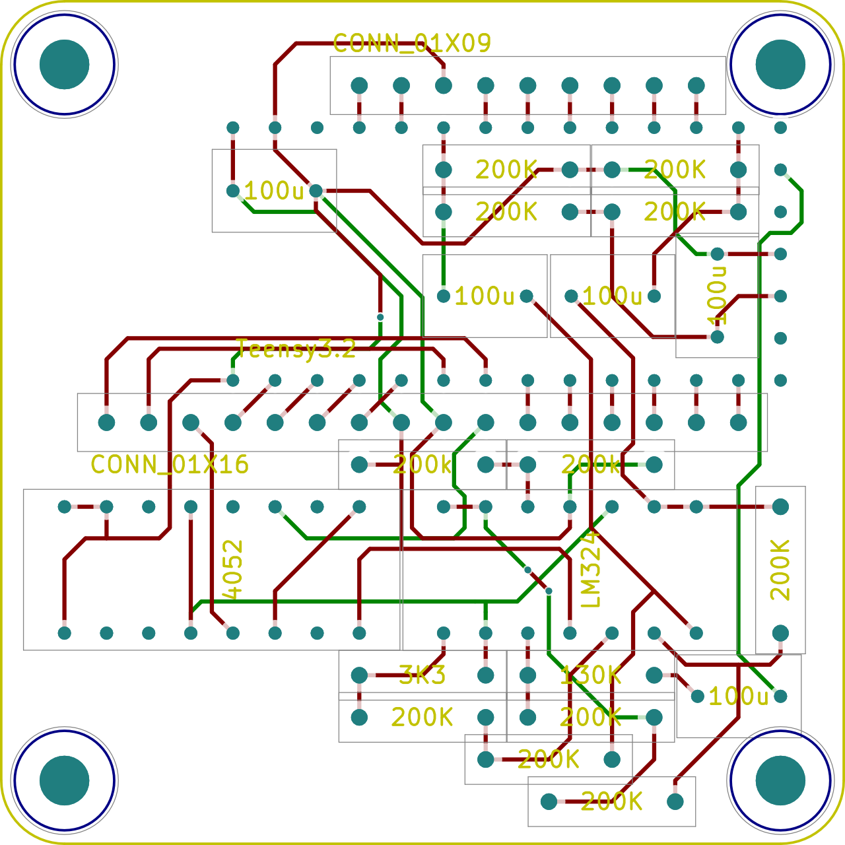
Documentation/Build_instructions/Step7_1.PNG
