ArthurAdmiraal/EISFlowSensing/Documentation/Build_instructions/Step7_2.PNG

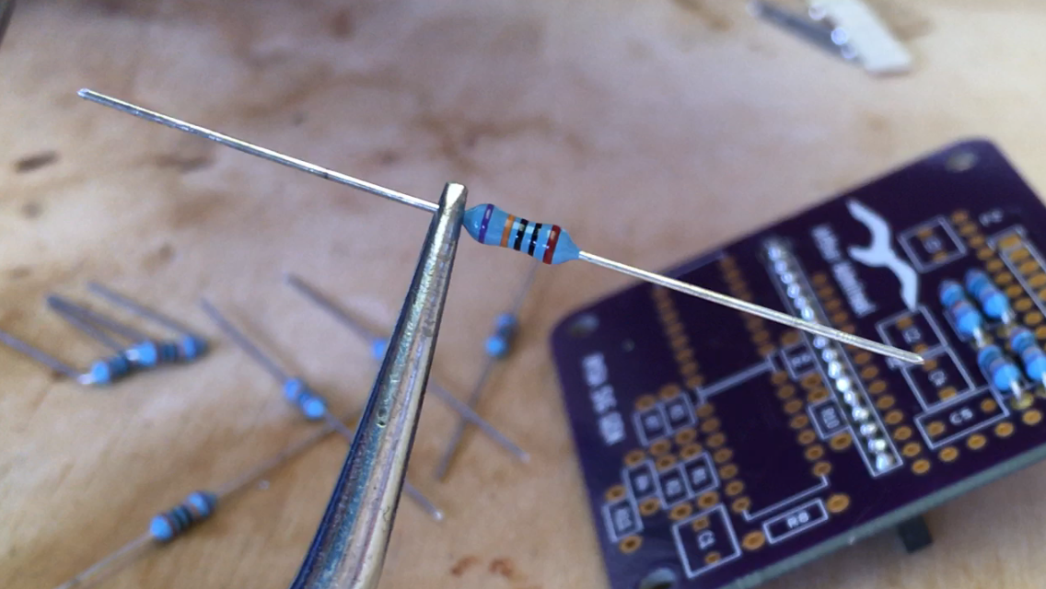
Documentation/Build_instructions/Step7_2.PNG
