ArthurAdmiraal/EISFlowSensing/Documentation/Build_instructions/Step7_3.PNG

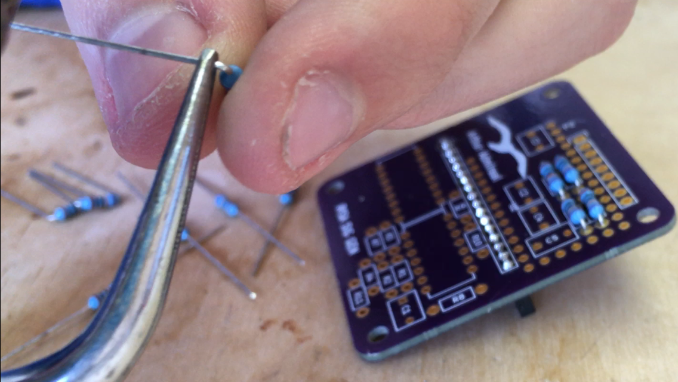
Documentation/Build_instructions/Step7_3.PNG
