ArthurAdmiraal/EISFlowSensing/Documentation/Build_instructions/Step7_4.PNG

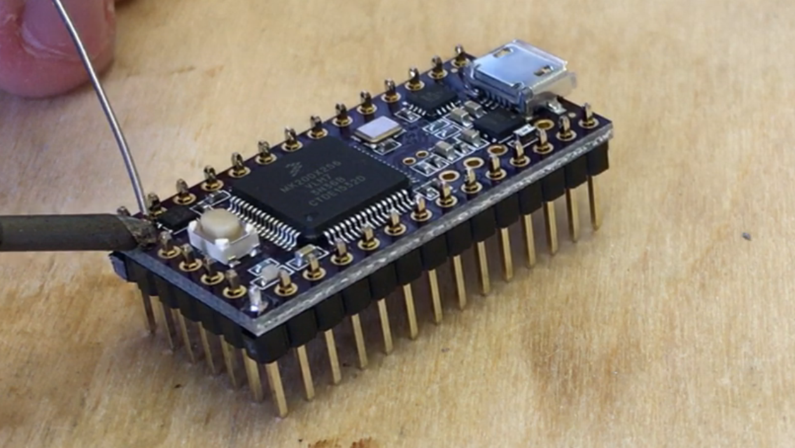
Documentation/Build_instructions/Step7_4.PNG
