ArthurAdmiraal/EISFlowSensing/Documentation/Build_instructions/Step7_5.PNG

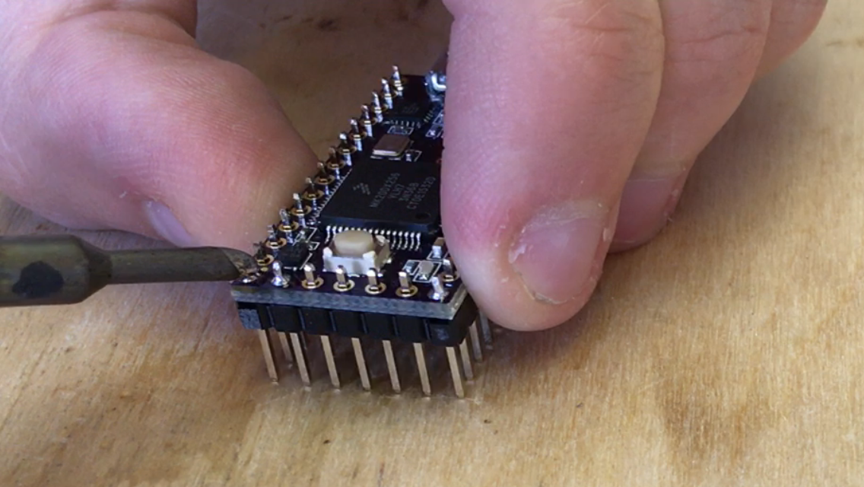
Documentation/Build_instructions/Step7_5.PNG
