ArthurAdmiraal/EISFlowSensing/Documentation/Build_instructions/Step7_6.PNG

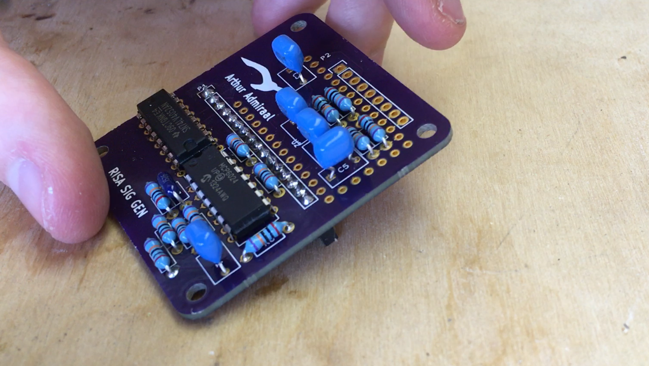
Documentation/Build_instructions/Step7_6.PNG
