ArthurAdmiraal/EISFlowSensing/Documentation/Build_instructions/Step8_1.JPG

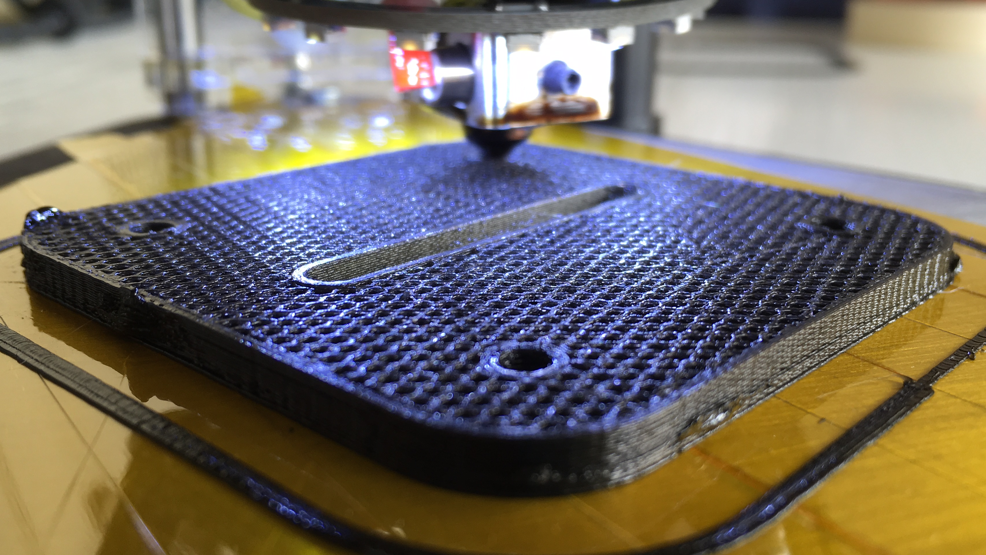
Documentation/Build_instructions/Step8_1.JPG
