ArthurAdmiraal/EISFlowSensing/Documentation/Build_instructions/Step8_2.PNG

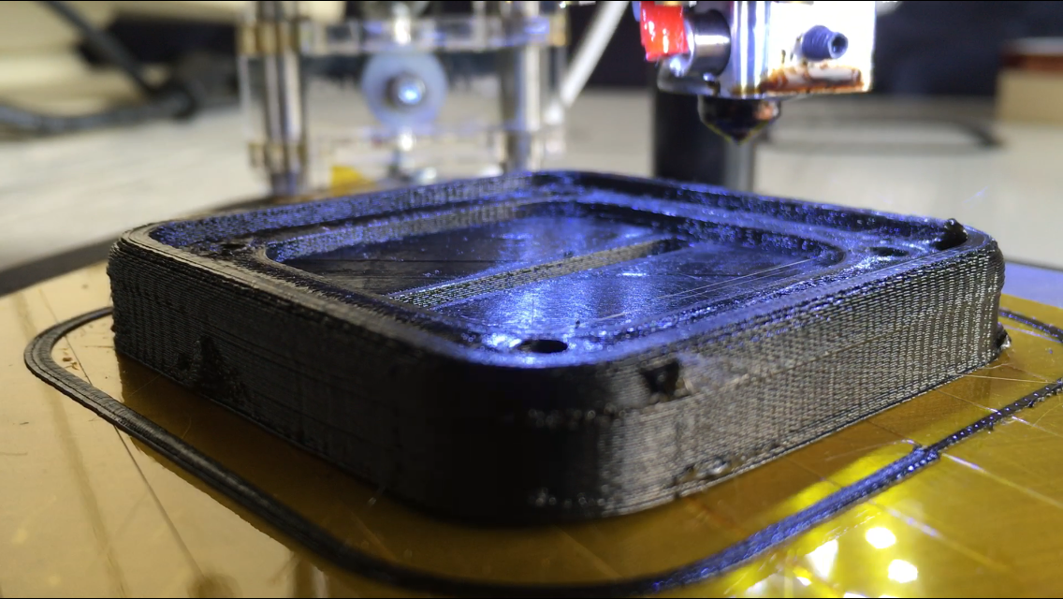
Documentation/Build_instructions/Step8_2.PNG
