ArthurAdmiraal/EISFlowSensing/Documentation/Build_instructions/Step8_3.png

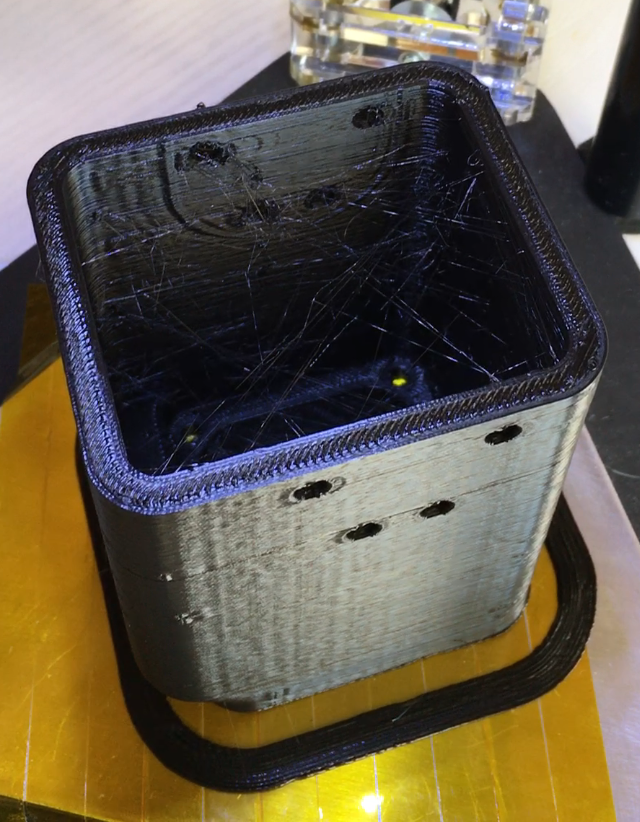
Documentation/Build_instructions/Step8_3.png
