ArthurAdmiraal/EISFlowSensing/Documentation/Render/BaseBuild.jpg

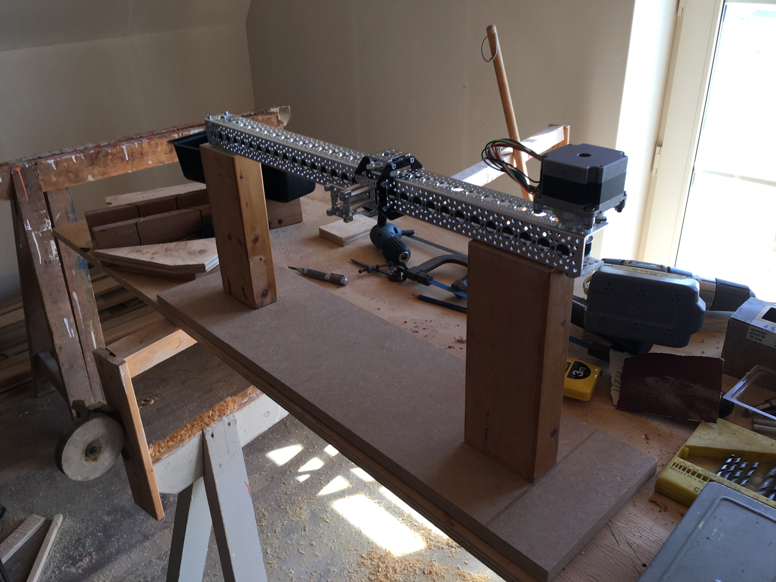
Documentation/Render/BaseBuild.jpg
