ArthurAdmiraal/EISFlowSensing/Documentation/Render/CakeTinConductivityTest.jpg

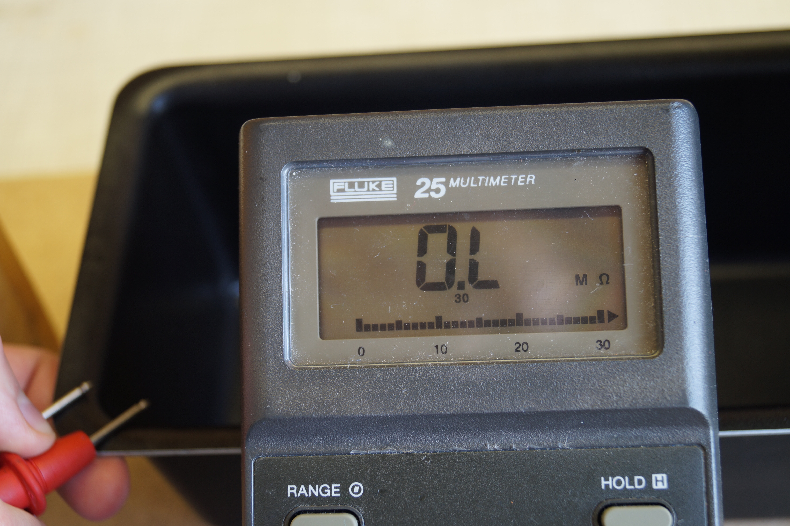
Documentation/Render/CakeTinConductivityTest.jpg
