ArthurAdmiraal/EISFlowSensing/Documentation/Render/Results.png

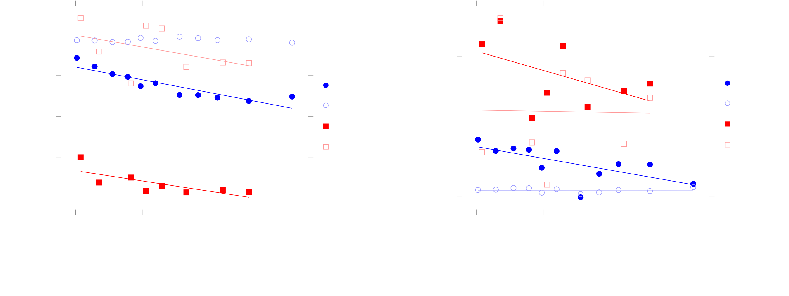
Documentation/Render/Results.png
