ArthurAdmiraal/EISFlowSensing/Documentation/Render/SigGenCurrentMeasurement.png

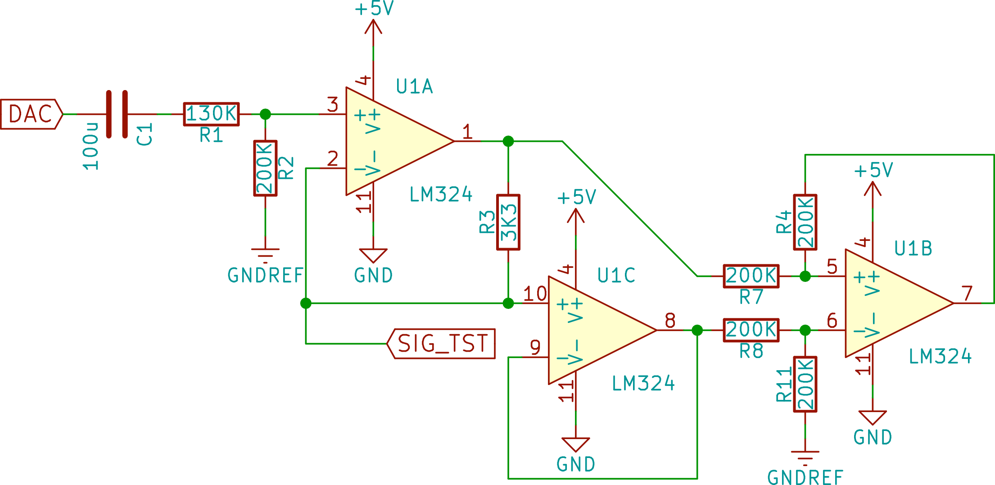
Documentation/Render/SigGenCurrentMeasurement.png
