ArthurAdmiraal/EISFlowSensing/Documentation/Render/TestSetupOne.jpg

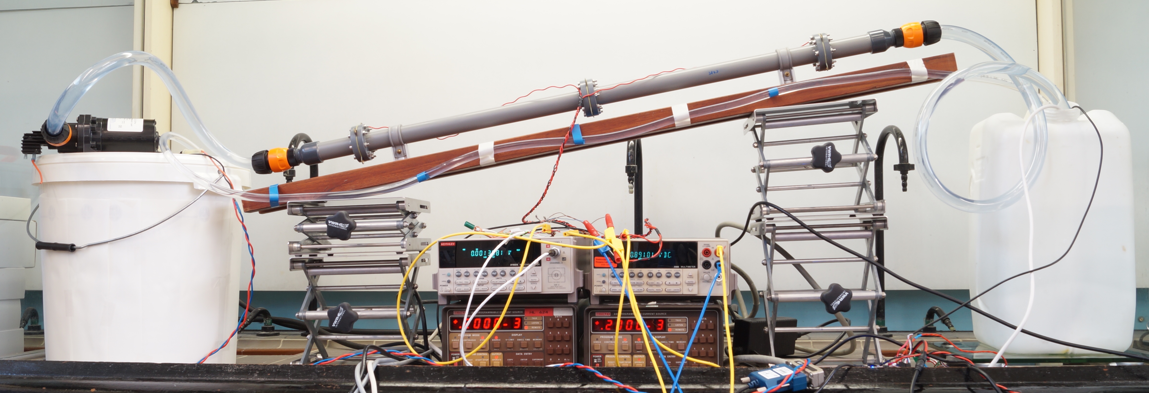
Documentation/Render/TestSetupOne.jpg
